ksr/p8x/hardware/control-card/kicad/README.md

# control-card -- KiCad

Generated by `generators/gen_kicad.py` from the canonical gen_eagle netlist
(`CARDS["control-card"]`), same standard as the memory card: 4-layer (F/B signals,
In1=GND, In2=VCC planes), a bypass cap above each IC, a labelled LED/jumper bank,
part values on silk. Routed with Freerouting. GENERATORS ARE CANON -- edit
`gen_kicad.py` and re-run `generators/build_kicad_card.sh control-card`.

| File | What |
|---|---|
| `p8x-control-card.kicad_pcb` | the board |
| `p8x-control-card.ses` | the Freerouting routing |
| `p8x-control-card-gerbers.zip` | orderable gerbers |
| `p8x-control-card-placement.pdf` | parts placement (refs+values) |
| `p8x-control-card-render-top.png` / `-3d.png` | renders |

Exotic parts use the closest standard KiCad footprint (flagged when built).
