ksr/p8x/fpga/tang-nano-20k/sdram/README.md

# SDRAM — Stage 0: does the in-package SDRAM work under the open flow?

The GW2AR-18's `R` is 64 Mbit of SDRAM in the same package, unused since the
microcode-compaction trick made it unnecessary for the 64K memory map. The
graphics framebuffer is the first thing that genuinely cannot fit in block RAM:
6 spare BSRAM blocks are 12288 bytes and the panel's own 480x272 needs 16320 at
even 1 bpp, so the current 240x136 2 bpp framebuffer is pixel-doubled to fill the
screen. Full resolution is an SDRAM project. This directory is the experiment.

## Finding 1: the SDRAM pads need NO `.cst` entries (verified 2026-08-17)

They are bonded inside the package, and **apicula/nextpnr special-cases the
magic port names**, exactly as Gowin EDA does. Verified by controlled experiment
rather than by reading about it:

| top-level port | result |
|---|---|
| `O_sdram_addr[10:0]` | placed, no constraint given |
| `O_notmagic_addr[10:0]` (same net, renamed) | `ERROR: Unconstrained IO` |

That control matters: nextpnr treats unconstrained IO as a hard error (it threw
exactly that for a mis-typed `led[4]`), so "placed without a constraint" can only
mean the name is recognised. A trivial design with all 55 SDRAM signals placed
clean at 30 IOBs for the control/address lines plus 32 `IOBUF`s for the data bus.

The magic names, which must appear verbatim on the top-level module:

```verilog
output        O_sdram_clk, O_sdram_cke, O_sdram_cs_n,
output        O_sdram_cas_n, O_sdram_ras_n, O_sdram_wen_n,
inout  [31:0] IO_sdram_dq,      // 32 bits wide, not 16
output [10:0] O_sdram_addr,
output [1:0]  O_sdram_ba,
output [3:0]  O_sdram_dqm
```

## Finding 2: it works (verified on hardware 2026-08-17)

`sdram_test.v` reports `SDRAM SEQ=0000 SPR=0000 PASS` on the board:

- 64 KB written and read back byte for byte, no errors
- a sparse pass touching one byte every 64 KB across the **whole 8 MB**, no
  errors -- so no address aliasing: rows, columns and banks are wired as
  expected and high addresses do not fold onto low ones
- refresh held throughout, the two passes being separated by the entire write
  phase

Costs, which was the other half of what stage 0 was for:

| | |
|---|---|
| LUT4 | 916 / 20736 (4%) -- controller **plus** test FSM **plus** UART |
| BSRAM | **0 / 46** |
| Fmax | 147 MHz against the 27 MHz it runs at |

The zero BSRAM is the important one. An SDRAM framebuffer does not add pressure
to a design already at 44/46 -- it *returns* the four blocks the current
framebuffer occupies, minus whatever a scanout line buffer needs (one block
holds a 2048-byte line, which is more than a 480-pixel line needs at any depth
we would pick).

### Bandwidth is not the constraint either

At 27 MHz the 32-bit bus is ~108 MB/s peak. Scanout needs:

| mode | bytes/frame | at 54.11 Hz | % of peak |
|---|---|---|---|
| 480x272 @ 4 bpp | 65,280 | 3.5 MB/s | 3% |
| 480x272 @ 8 bpp | 130,560 | 7.1 MB/s | 7% |

So the drawing engine keeps well over 90% of the bus even at 256 colours. What
is left to prove is **latency**, not throughput: SDRAM cannot promise a byte on
demand the way block RAM does, and a scanout cannot stall. That is stage 1.

## Finding 3: a scanout can live off SDRAM (verified on hardware 2026-08-17)

`sdram_video_test.v` puts a 480x272 8-bpp image on the panel, fetched line by
line from SDRAM. Confirmed on the board: the picture is correct -- border,
both diagonals and the fine horizontal ramp all as designed, so line addressing,
stride and the 32-bit byte lanes are all right.

| | stage 1 | today's BSRAM framebuffer |
|---|---|---|
| LUT4 | 835 / 20736 (4%) | -- |
| BSRAM | **1** (the line buffer) | **4** |
| Fmax | 200 MHz | -- |

**Four times the resolution and 64 times the colours, for three FEWER block
RAMs.** That inverts the trade-off this started from: the SDRAM path is not a
way to spend resources to get resolution, it is a way to get resolution and hand
resources back to a design that was at 44/46 and on a placement cliff.

(The cliff itself turned out to have a second, larger cause that had nothing to
do with graphics — the SD sector buffer inferring 4,096 flip-flops. With both
fixed the `lcd` build sits at 7226/20736 LUT4 and 42/46 BSRAM. See
[HANDOFF.md](HANDOFF.md).)

### Still to confirm

The `underruns` counter is the real measurement and has only been eyeballed, not
watched over a long run. It should be read as "UR=0000 with FR climbing" over
minutes, not seconds, before this is called settled -- and re-checked once a
drawing engine is competing for the same bus, which is the case that matters.

Stage 1 was also NOT simulated before loading, unlike stage 0. That is a gap: the
stage 0 bench caught two real bugs, and the same discipline should be applied
here before any of this is merged toward the P8X design.

## What this does and does not prove

It proves the toolchain will *wire up* the SDRAM. It says nothing yet about
whether we can meet its timing, which is the actual risk: SDRAM has refresh, row
activation and CAS latency, so unlike block RAM it cannot promise a byte on
demand — and a video scanout cannot stall. That is what the rest of Stage 0 and
Stage 1 are for.

## Reference

`nand2mario/sdram-tang-nano-20k` (Apache 2.0) is a known-good 32-bit controller
for this exact board: 64.8 MHz, 4-cycle read latency, byte-addressable interface.
It targets Gowin EDA and instantiates the `Gowin_rPLL` IP wrapper, so an open-flow
port would instantiate the `rPLL` primitive directly.
