ksr/p8x/BACKLOG-DONE.md

# P8X Backlog — Completed

<!-- migrated from BACKLOG.md 2026-09-14 (category review: [x] done items belong here) -->

<!-- 2026-10-02: hardware items closed by the KiCad flow, and the 2026-09-16 overnight batch -->

- [x] **Publish the project website (2026-10-02).** `website/` builds the site
      from these documents (MkDocs + Material; `sh website/build.sh publish` is a
      strict build), and `.github/workflows/website.yml` builds it on every push to
      `main` and, with deploy switched on (2026-10-02), publishes it to
      https://p8x.cottageworker.com. The visitor status page is
      `docs/p8x-status.md`; keep it current with BACKLOG.md.
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
