ksr/p8x/GLOSSARY.md

# P8X Glossary — acronyms & signals

A reference for the abbreviations, signal names, and register/bus terms used
across the P8X project. Authoritative sources where a term has one:
- control word / opcodes → `microcode/genucode.py`
- bus pinout → `hardware/backplane/p8x-bus-definition.md`
- monitor/BIOS ABI → `docs/p8x-monitor.md`
- parts → `hardware/p8x-bom.csv` (from `generators/gen_bom.py`)

---
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
