ksr/p8x/hardware/alu-card/kicad/p8x-alu-card-render-top.png

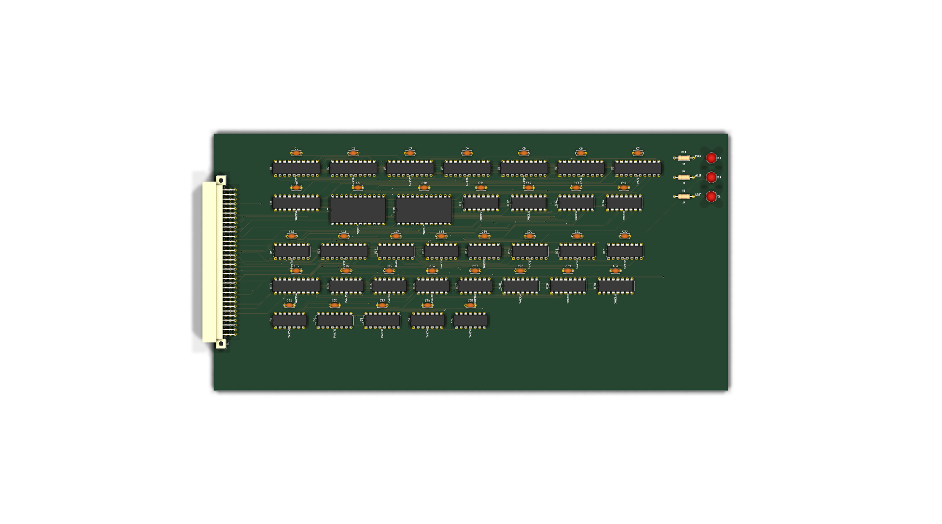
hardware/alu-card/kicad/p8x-alu-card-render-top.png
