ksr/p8x/hardware/backplane/kicad/p8x-backplane-render-3d.png

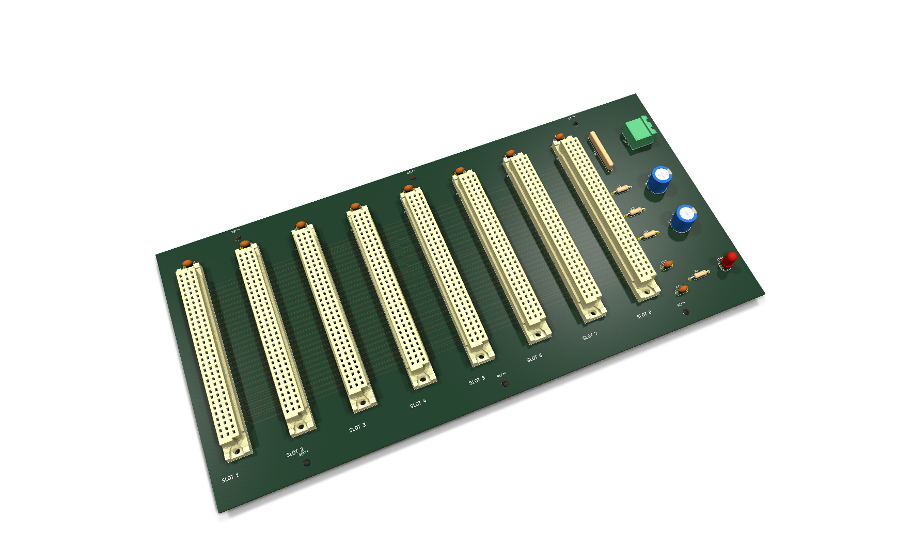
hardware/backplane/kicad/p8x-backplane-render-3d.png
