ksr/p8x/hardware/memory-card/kicad/p8x-memory-card-render-3d.png

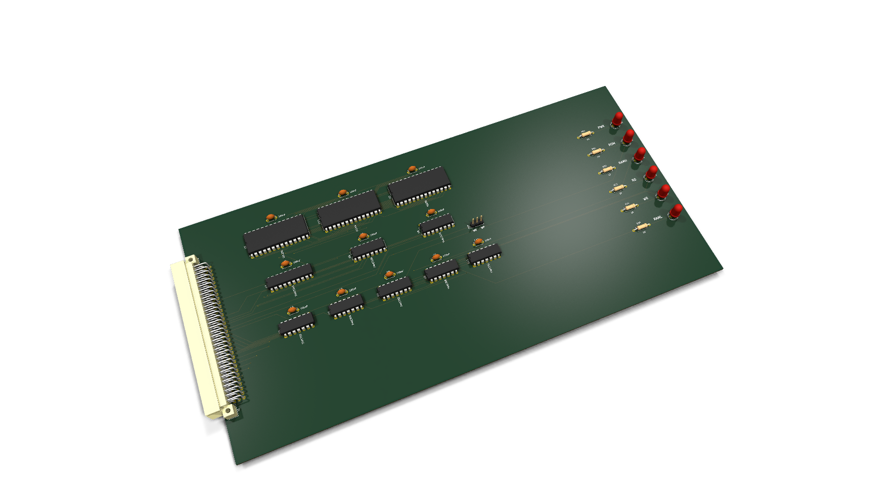
hardware/memory-card/kicad/p8x-memory-card-render-3d.png
