ksr/p8x/hardware/parked/peripheral-card/kicad/p8x-peripheral-card-render-3d.png

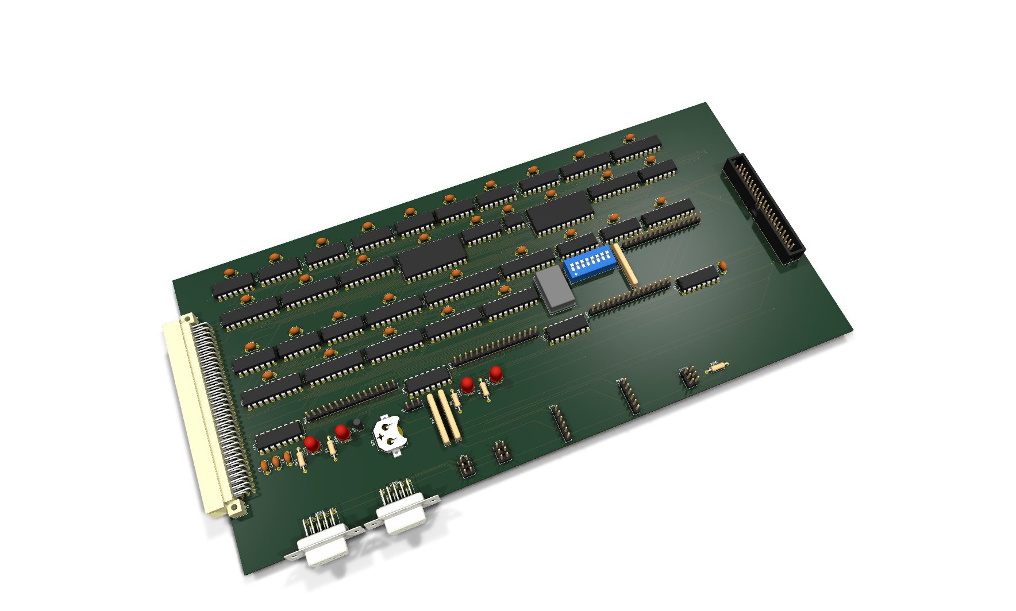
hardware/parked/peripheral-card/kicad/p8x-peripheral-card-render-3d.png
