ksr/p8x/hardware/regbank-card/kicad/p8x-regbank-card-render-top.png

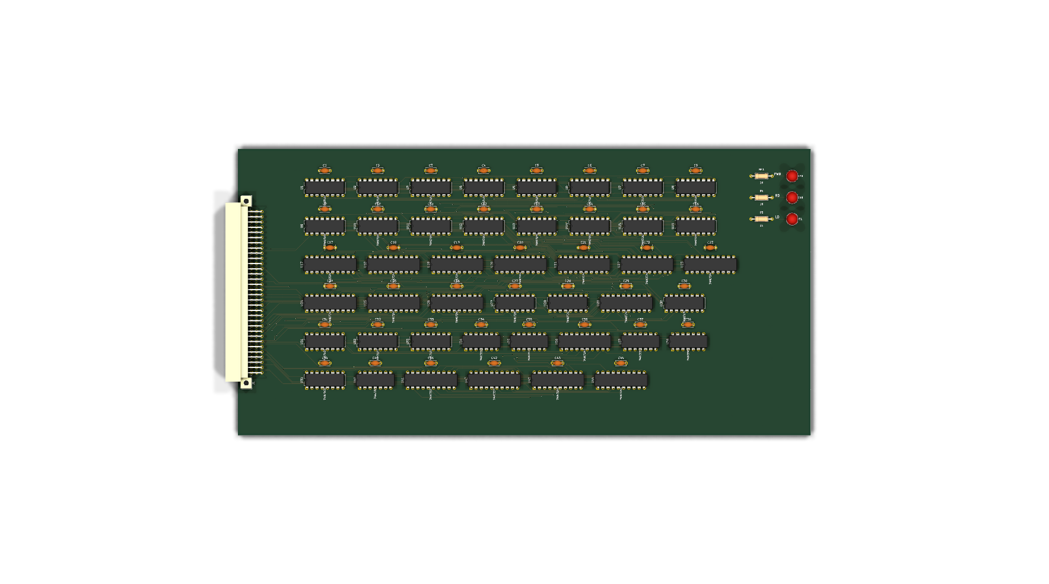
hardware/regbank-card/kicad/p8x-regbank-card-render-top.png
