ksr/p8x/website/p8x-collage.jpg

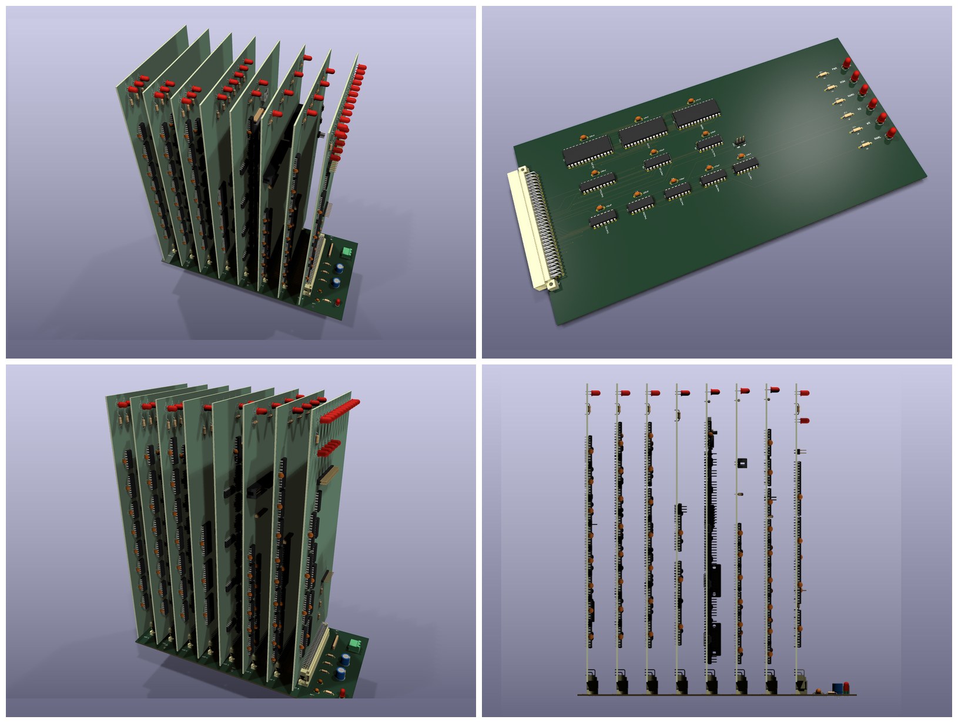
website/p8x-collage.jpg
