ksr/p8x/hardware/cf-card/p8x-cf-card-placement.pdf

U1 74HCT245 | C1 | U2 74HCT30 | C2 | U3 74HCT138 | C3 | U4 74HCT138 | C4 | U5 74HCT14 | C5 | U6 74HCT10 | C6 | U7 74HCT10 | C7 | U8 74HCT08 | C8

# P8X CF-IDE CARD REV A - 8-BIT TRUE IDE AT 0xFF10

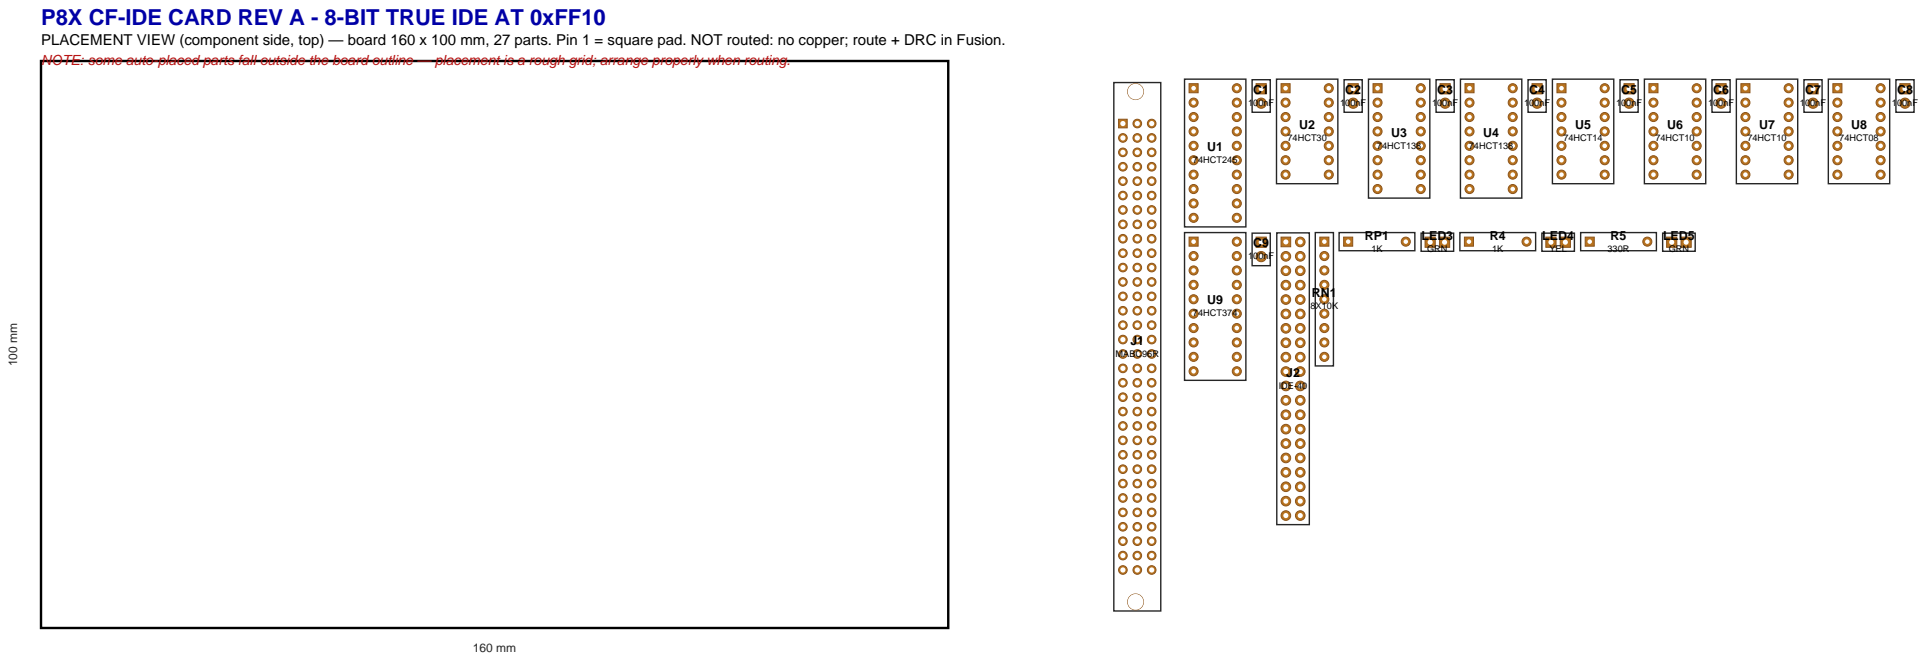
[picture p26: page 1]

PLACEMENT VIEW (component side, top) — board 160 x 100 mm, 27 parts. Pin 1 = square pad. NOT routed: no copper; route + DRC in Fusion.
NOTE: some auto-placed parts fall outside the board outline — placement is a rough grid; arrange properly when routing.

U9 74HCT374 | C9 | | 1K | LED3 GRN | 1K | LED4 YEL | 330R | LED5 GRN
