ksr/p8x/hardware/control-card/p8x-control-card-placement.pdf

U1 74HCT161 | C2 | U2 74HCT14 | C3 | U3 74HCT74 | C4 | U4 74HCT00 | C5 | U5 74HCT08 | C6 | U6 74HCT32 | C7 | U7 74HCT377 | C8 | U8 74HCT138 | C9

# P8X CONTROL/MICROCODE CARD REV B

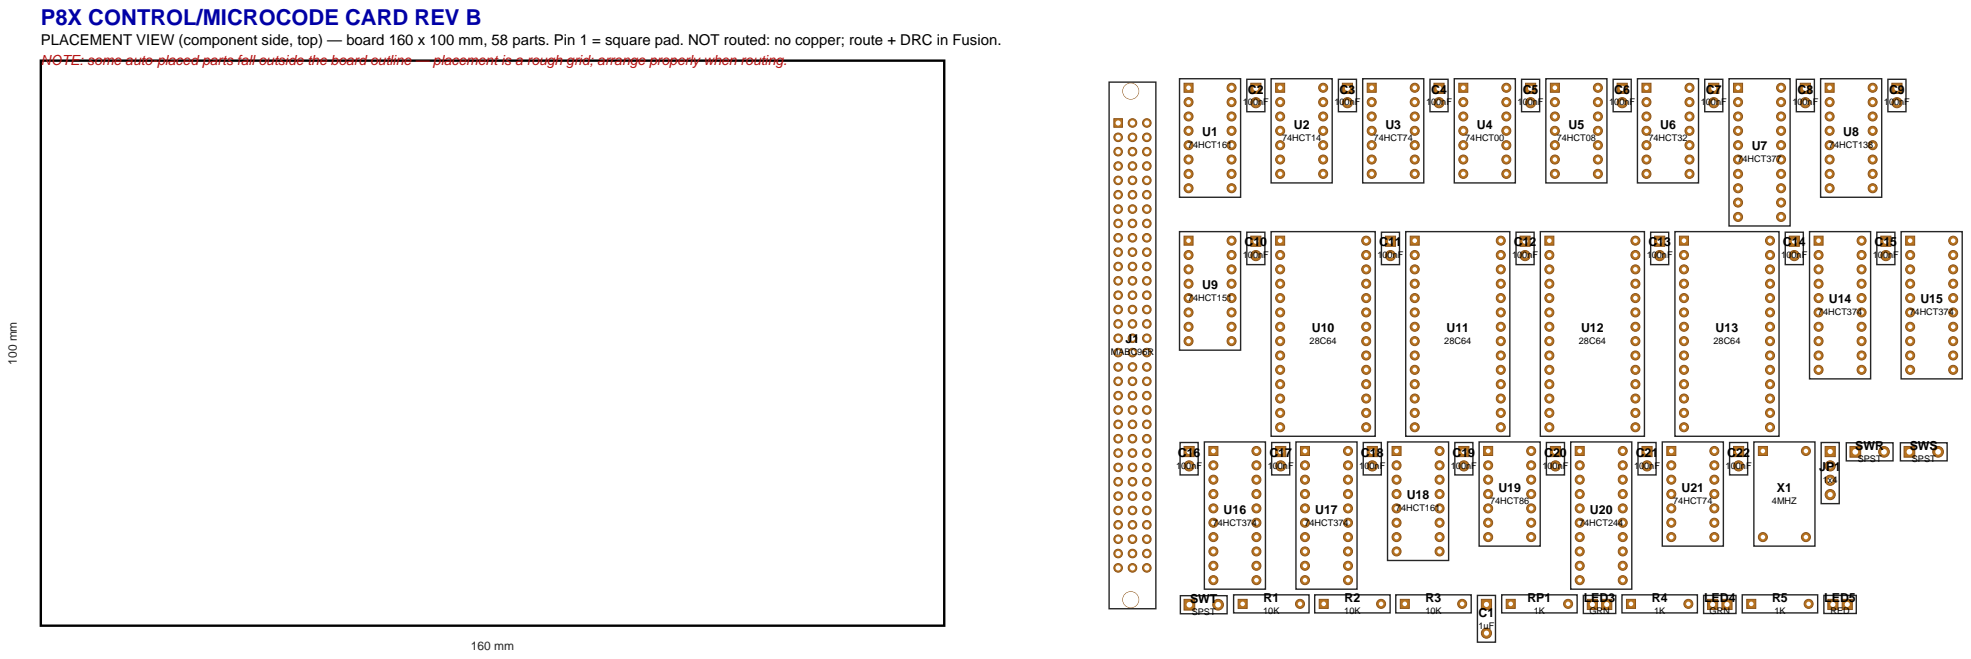
[picture p27: page 1]

PLACEMENT VIEW (component side, top) — board 160 x 100 mm, 58 parts. Pin 1 = square pad. NOT routed: no copper; route + DRC in Fusion.
NOTE: some auto-placed parts fall outside the board outline — placement is a rough grid; arrange properly when routing.

U9 74HCT151 | C10 | U10 28C64 | C11 | | U11 28C64 | C12 | U12 28C64 | C13 | U13 28C64 | C14 | 74HCT374 | U14 | C15 | 74HCT374 | U15
