ksr/p8x/hardware/control-card/p8x-control-card-schematic.pdf

# P8X CONTROL/MICROCODE CARD REV B - traditional wiring (auto-drafted)

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

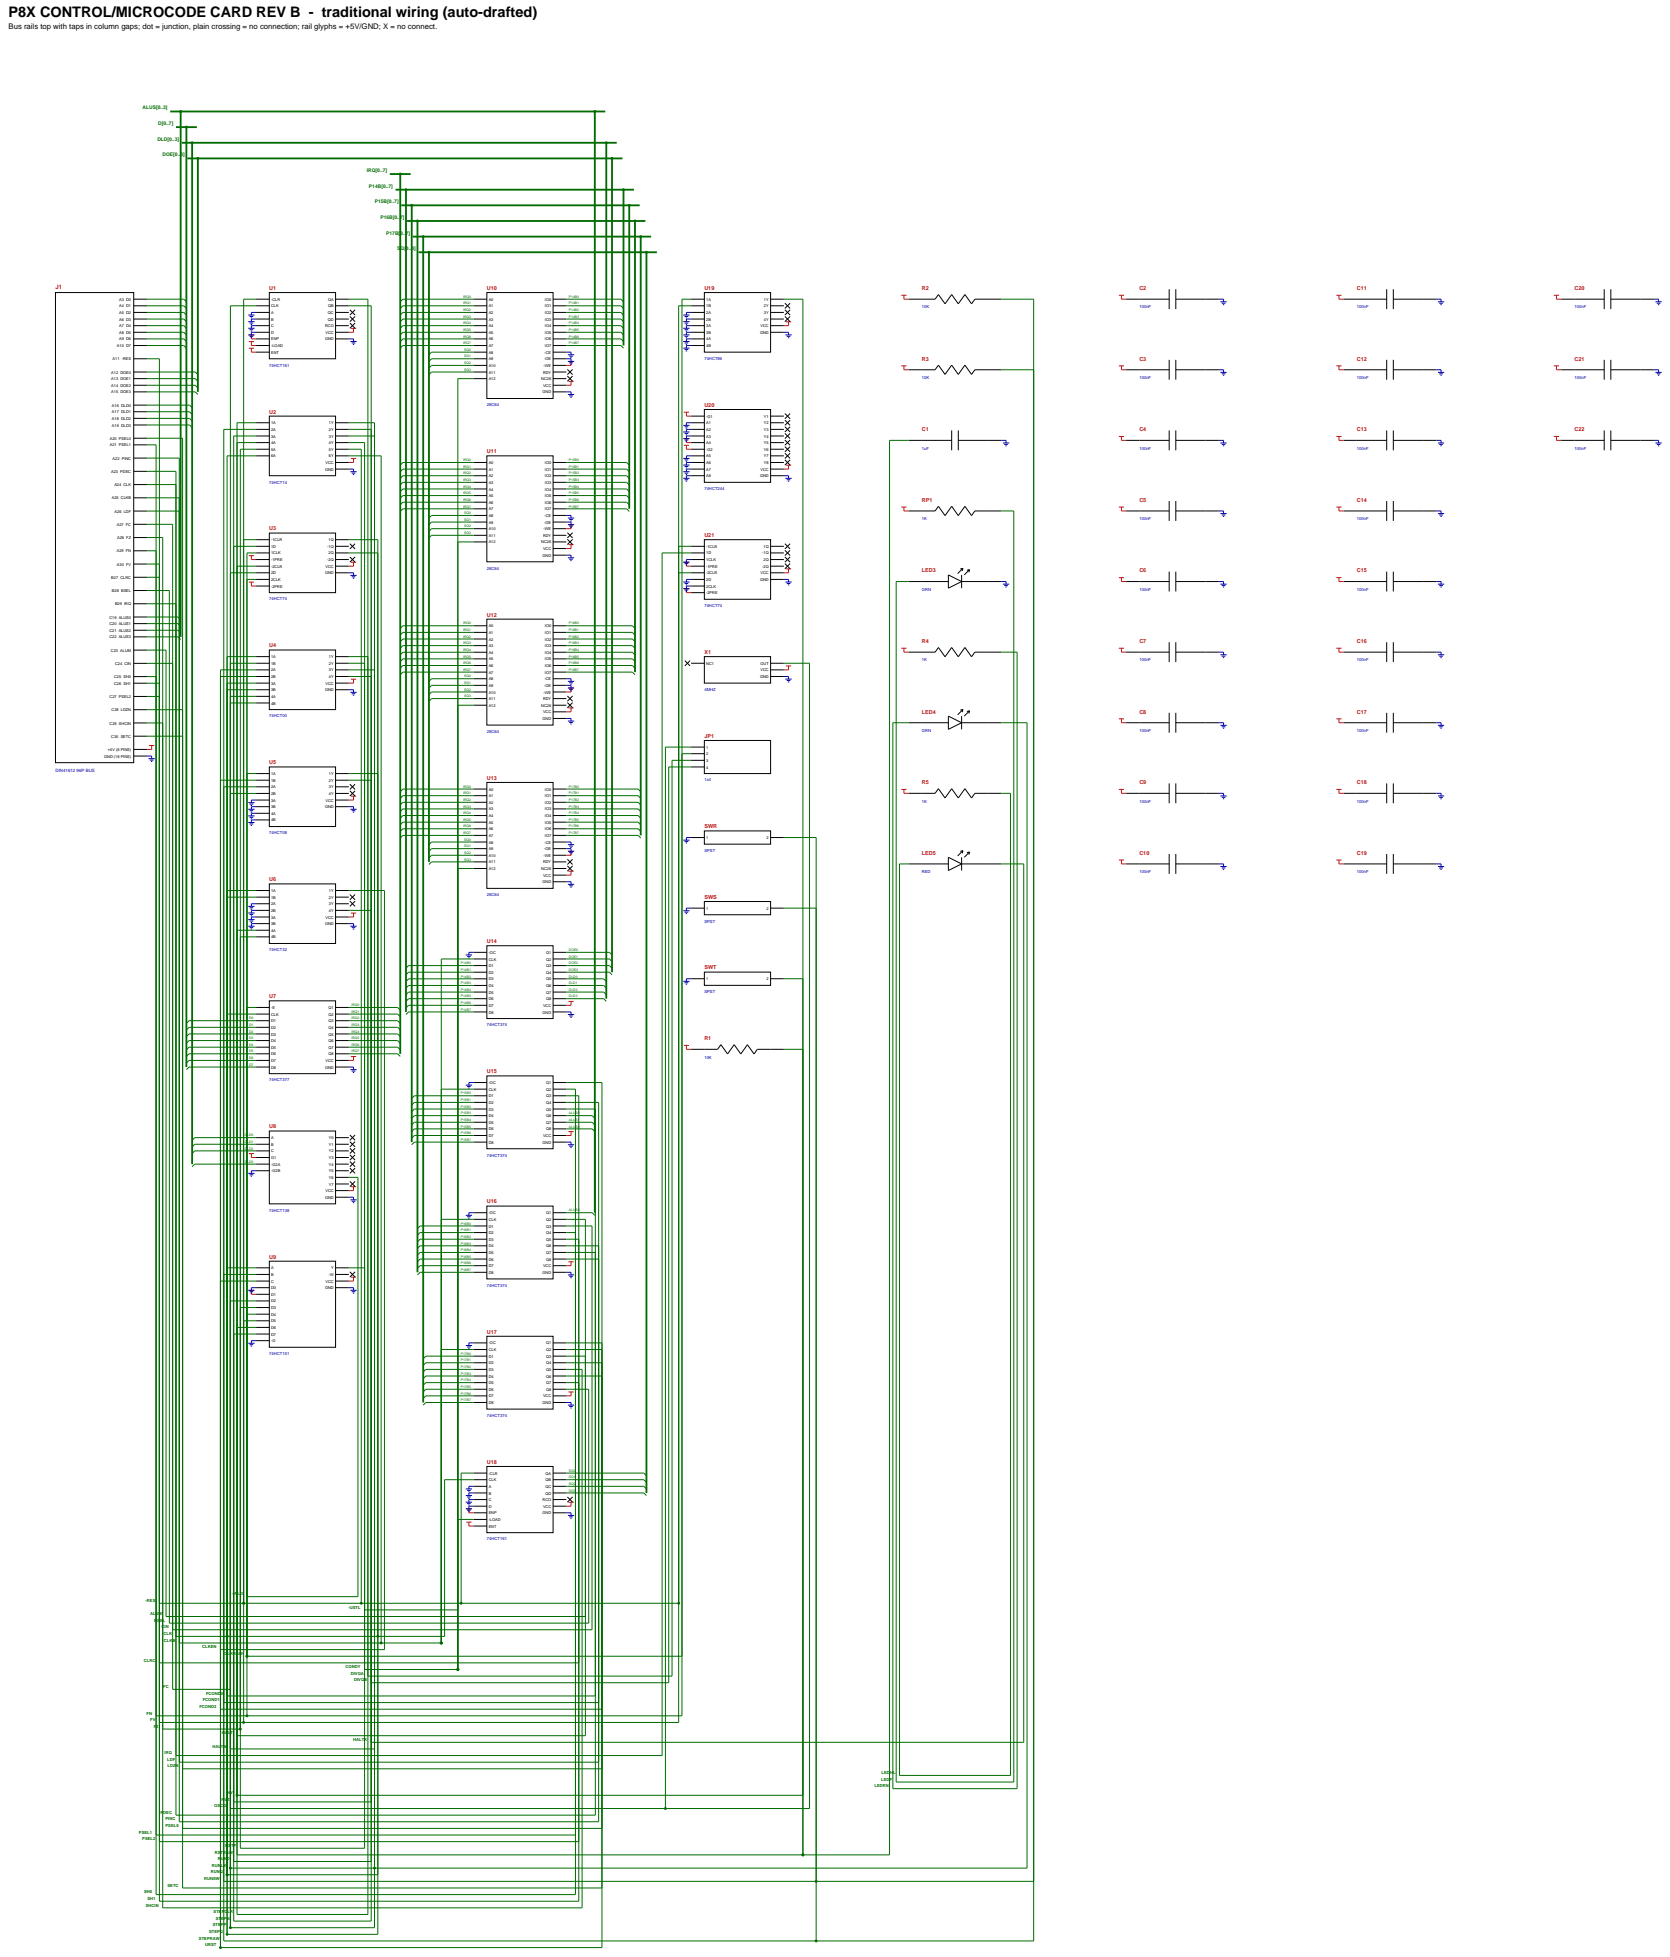
[picture p28: page 1]

CLKEN

CONDY DIVQA DIVQB
