ksr/p8x/hardware/io-card/p8x-io-card-placement.pdf

U1 74HCT30 | C6 | U2 74HCT138 | C7 | U3 74HCT138 | C8 | U4 74HCT138 | C9 | U5 74HCT32 | C10 | U6 74HCT08 | C11 | U7 74HCT161 | C12 | U8 MAX232 | C13

# P8X I/O CARD REV A - ACIA + SWITCHES + LEDS + BUS MONITOR

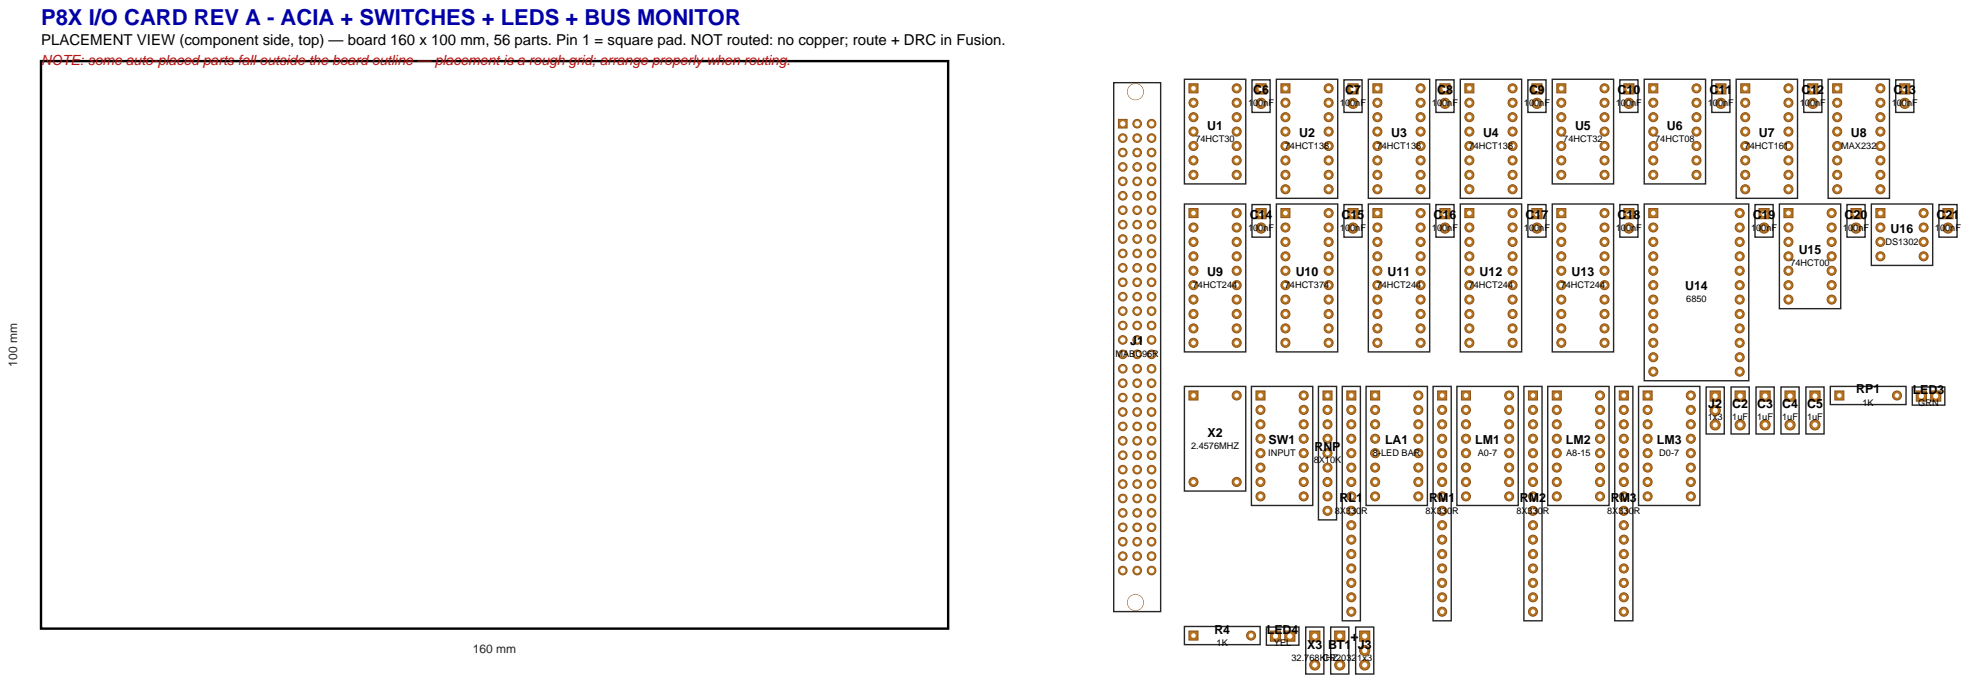
[picture p29: page 1]

PLACEMENT VIEW (component side, top) — board 160 x 100 mm, 56 parts. Pin 1 = square pad. NOT routed: no copper; route + DRC in Fusion.
NOTE: some auto-placed parts fall outside the board outline — placement is a rough grid; arrange properly when routing.

U9 74HCT244 | U10 74HCT374 | U11 74HCT244 | U12 74HCT244 | U13 74HCT244 | U14 6850 | U15 74HCT00 | U16 DS1302

C14 | C15 | C16 | C17 | C18 | C19 | C20 | C21
100nF | 100nF | 100nF | 100nF | 100nF | 100nF | 100nF | 100nF

X2 2.4576MHZ | SW1 | LA1 8-LED BAR | | LM1 A0-7 | LM2 A8-15 | | | LM3 D0-7 | J2 | C2 | C3 | C4 | C5 | RP1 1K | GRN
