ksr/p8x/hardware/led-card/p8x-led-card-placement.pdf

## P8X LED OUTPUT CARD (test - write-only 8 LEDs at $FF0C)

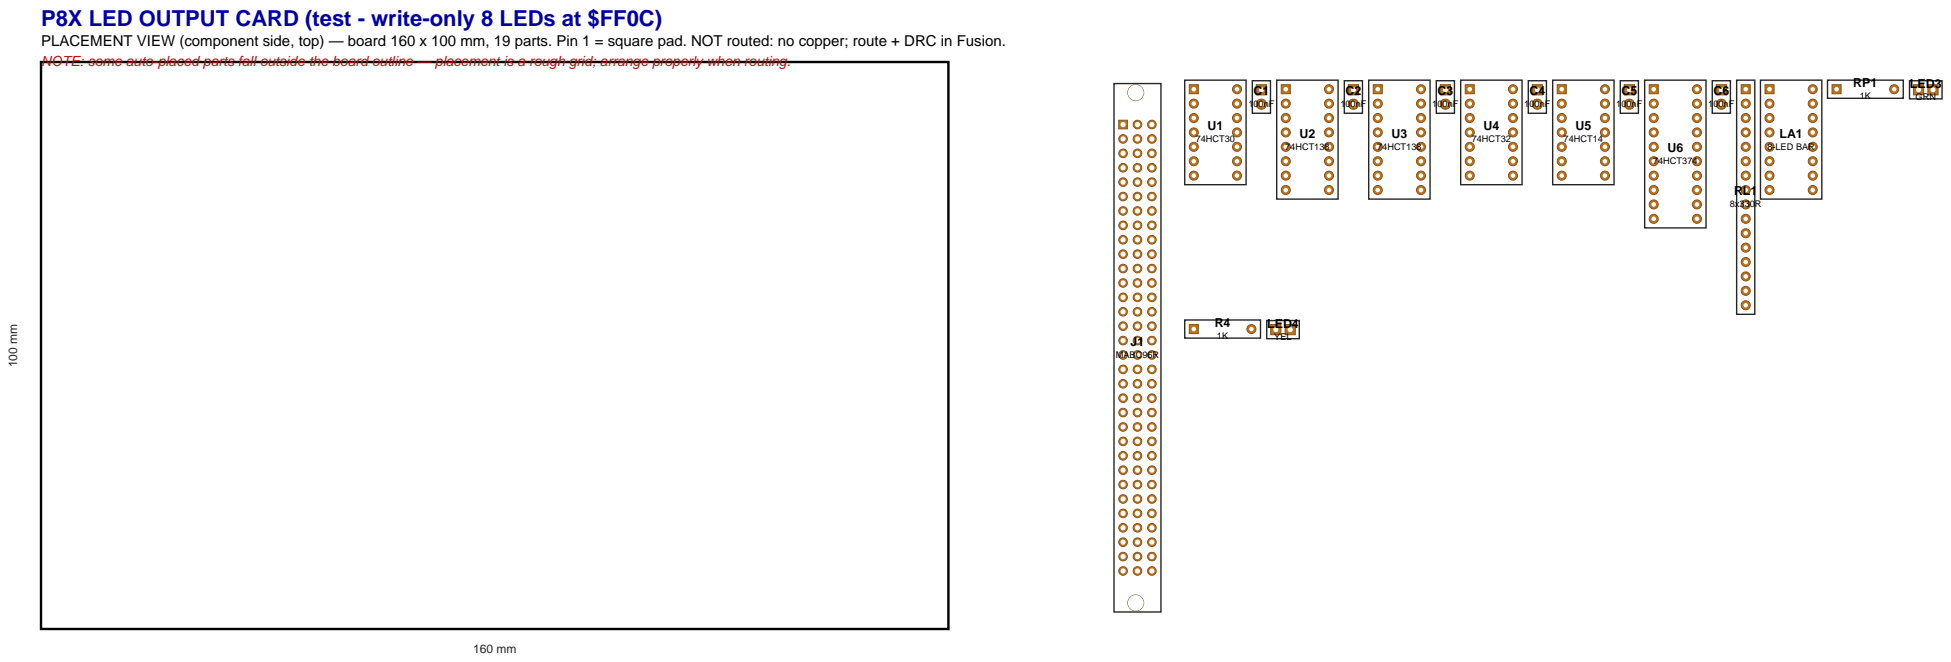
[picture p30: page 1]

PLACEMENT VIEW (component side, top) — board 160 x 100 mm, 19 parts. Pin 1 = square pad. NOT routed: no copper; route + DRC in Fusion.
NOTE: some auto-placed parts fall outside the board outline — placement is a rough grid; arrange properly when routing.

U1 74HCT30 | C1 | U2 74HCT138 | C2 | U3 74HCT138 | C3 | U4 74HCT32 | C4 | U5 74HCT14 | C5 | U6 74HCT374 | C6 | LA1 8-LED BAR | RP1 1K | LED3
