ksr/p8x/hardware/memory-card/p8x-memory-card-placement.pdf

U1 28C256 | C1 | U2 62256 | C2 | 74HCT245 | U3 | C3 | U4 74HCT30 | C4 | 74HCT138 | U5 | C5 | 74HCT138 | U6 | C6 | U7 74HCT00 | C7 | U8 74HCT32

# P8X MEMORY CARD REV E

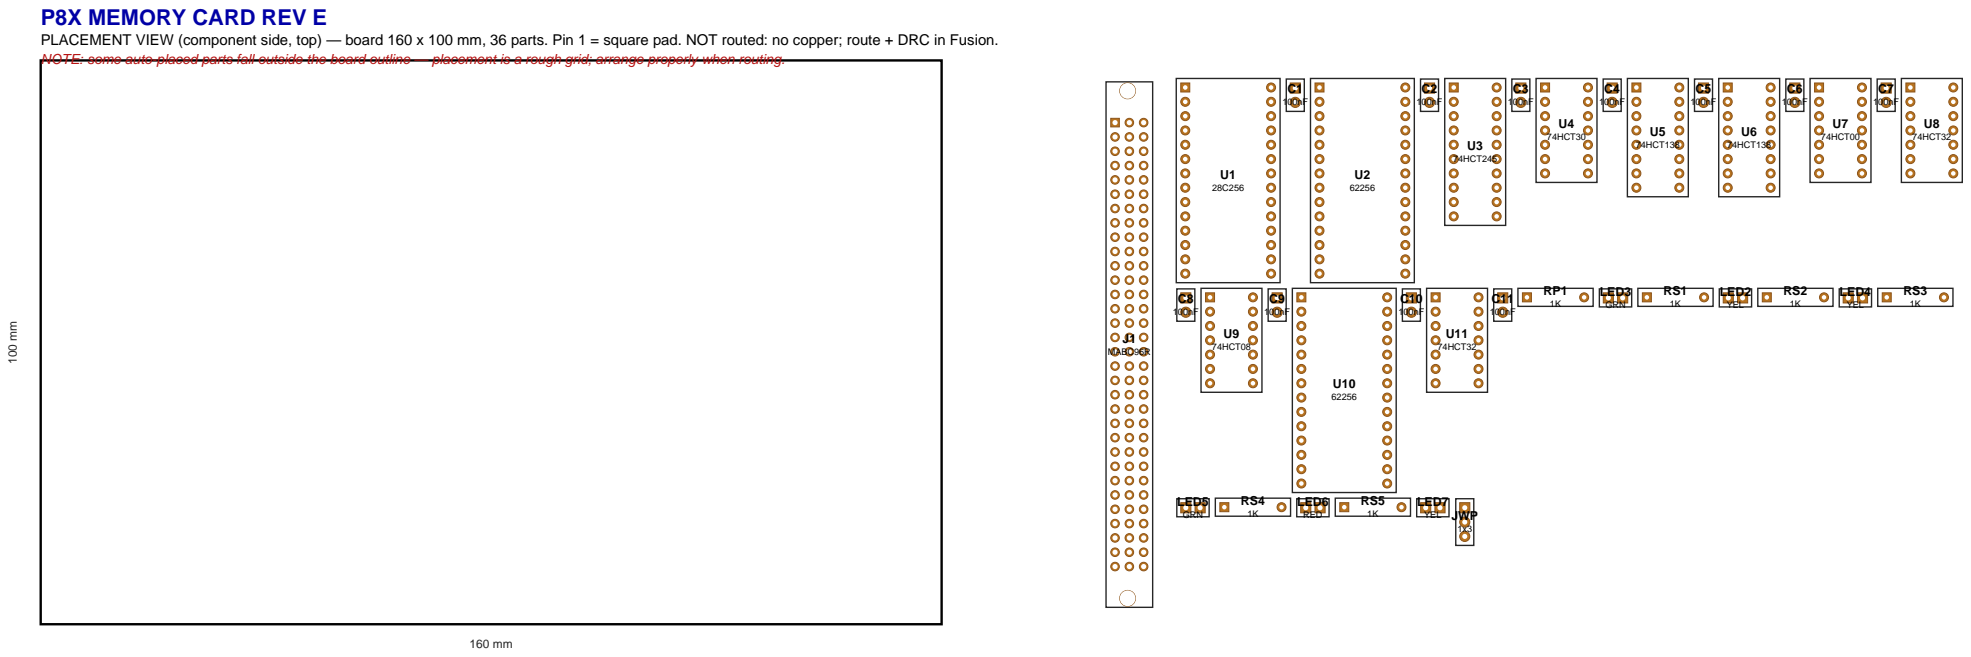
[picture p31: page 1]

PLACEMENT VIEW (component side, top) — board 160 x 100 mm, 36 parts. Pin 1 = square pad. NOT routed: no copper; route + DRC in Fusion.
NOTE: some auto-placed parts fall outside the board outline — placement is a rough grid; arrange properly when routing.
