ksr/p8x/hardware/regbank-card/p8x-regbank-card-placement.pdf

U1 74HCT169 | C1 | U2 74HCT169 | C2 | U3 74HCT169 | C3 | U4 74HCT169 | C4 | U5 74HCT169 | C5 | U6 74HCT169 | C6 | U7 74HCT169 | C7 | U8 74HCT169 | C8
C9 | C10 | C11 | C12 | C13 | C14 | C15 | C16

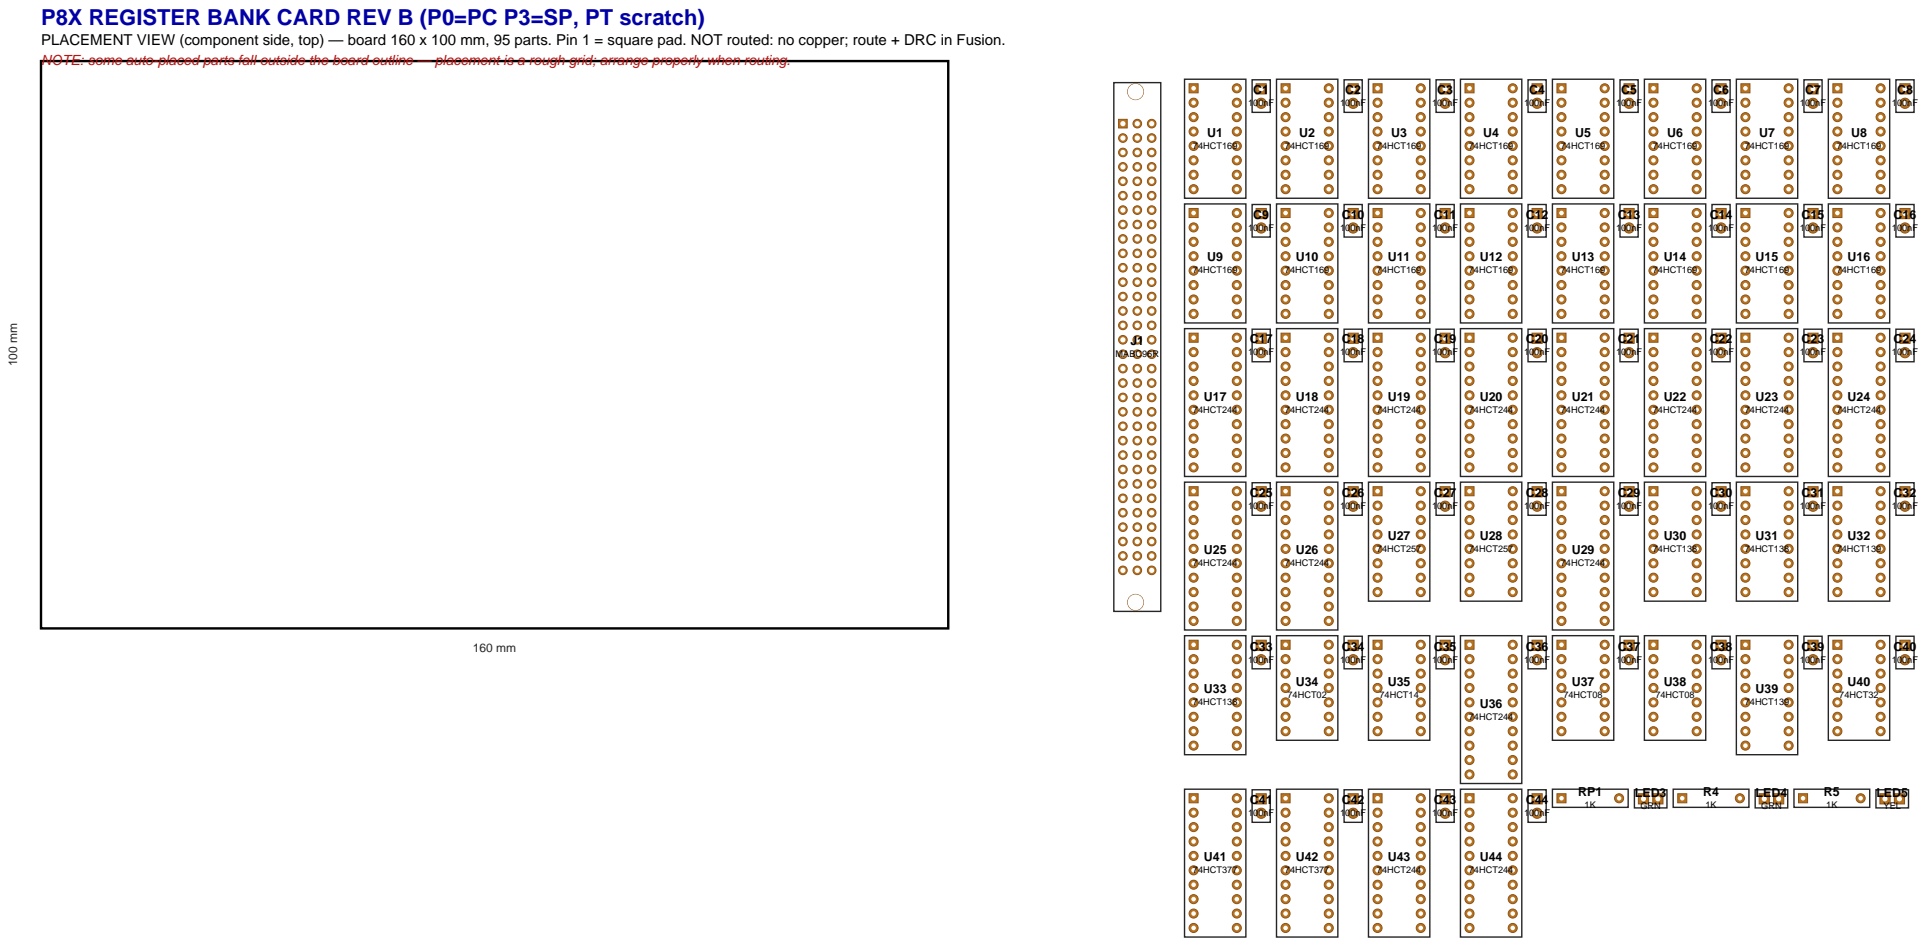
[picture p32: page 1]

P8X REGISTER BANK CARD REV B (P0=PC P3=SP, PT scratch)
PLACEMENT VIEW (component side, top) — board 160 x 100 mm, 95 parts. Pin 1 = square pad. NOT routed: no copper; route + DRC in Fusion.
NOTE: some auto-placed parts fall outside the board outline — placement is a rough grid; arrange properly when routing.

U9 74HCT169 | U10 74HCT169 | U11 74HCT169 | U12 74HCT169 | U13 74HCT169 | U14 74HCT169 | U15 74HCT169 | U16 74HCT169

U17 74HCT244 | C17 | U18 74HCT244 | C18 | U19 74HCT244 | C19 | U20 74HCT244 | C20 | U21 74HCT244 | C21 | U22 74HCT244 | C22 | U23 74HCT244 | C23 | U24 74HCT244 | C24

C25 | C26 | C27 | C28 | C29 | C30 | C31 | C32
100nF | 100nF | 100nF | 100nF | 100nF | 100nF | 100nF

U25 74HCT244 | U26 74HCT244 | U27 74HCT257 | U28 74HCT257 | U29 74HCT244 | U30 74HCT138 | U31 74HCT138 | U32 74HCT139

U33 74HCT138 | C33 | U34 74HCT02 | C34 | U35 74HCT14 | C35 | U36 74HCT244 | C36 | U37 74HCT08 | C37 | U38 74HCT08 | C38 | U39 74HCT139 | C39 | U40 74HCT32 | C40

U41 74HCT377 | C41 | U42 74HCT377 | C42 | U43 74HCT244 | C43 | U44 74HCT244 | C44 | 1K | LED3 GRN | 1K | LED4 GRN | 1K | LED5 YEL
