ksr/p8x/hardware/regbank-card/p8x-regbank-card-schematic.pdf

P8X REGISTER BANK CARD REV B (P0=PC P3=SP, PT scratch) - traditional wiring (auto-drafted)

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

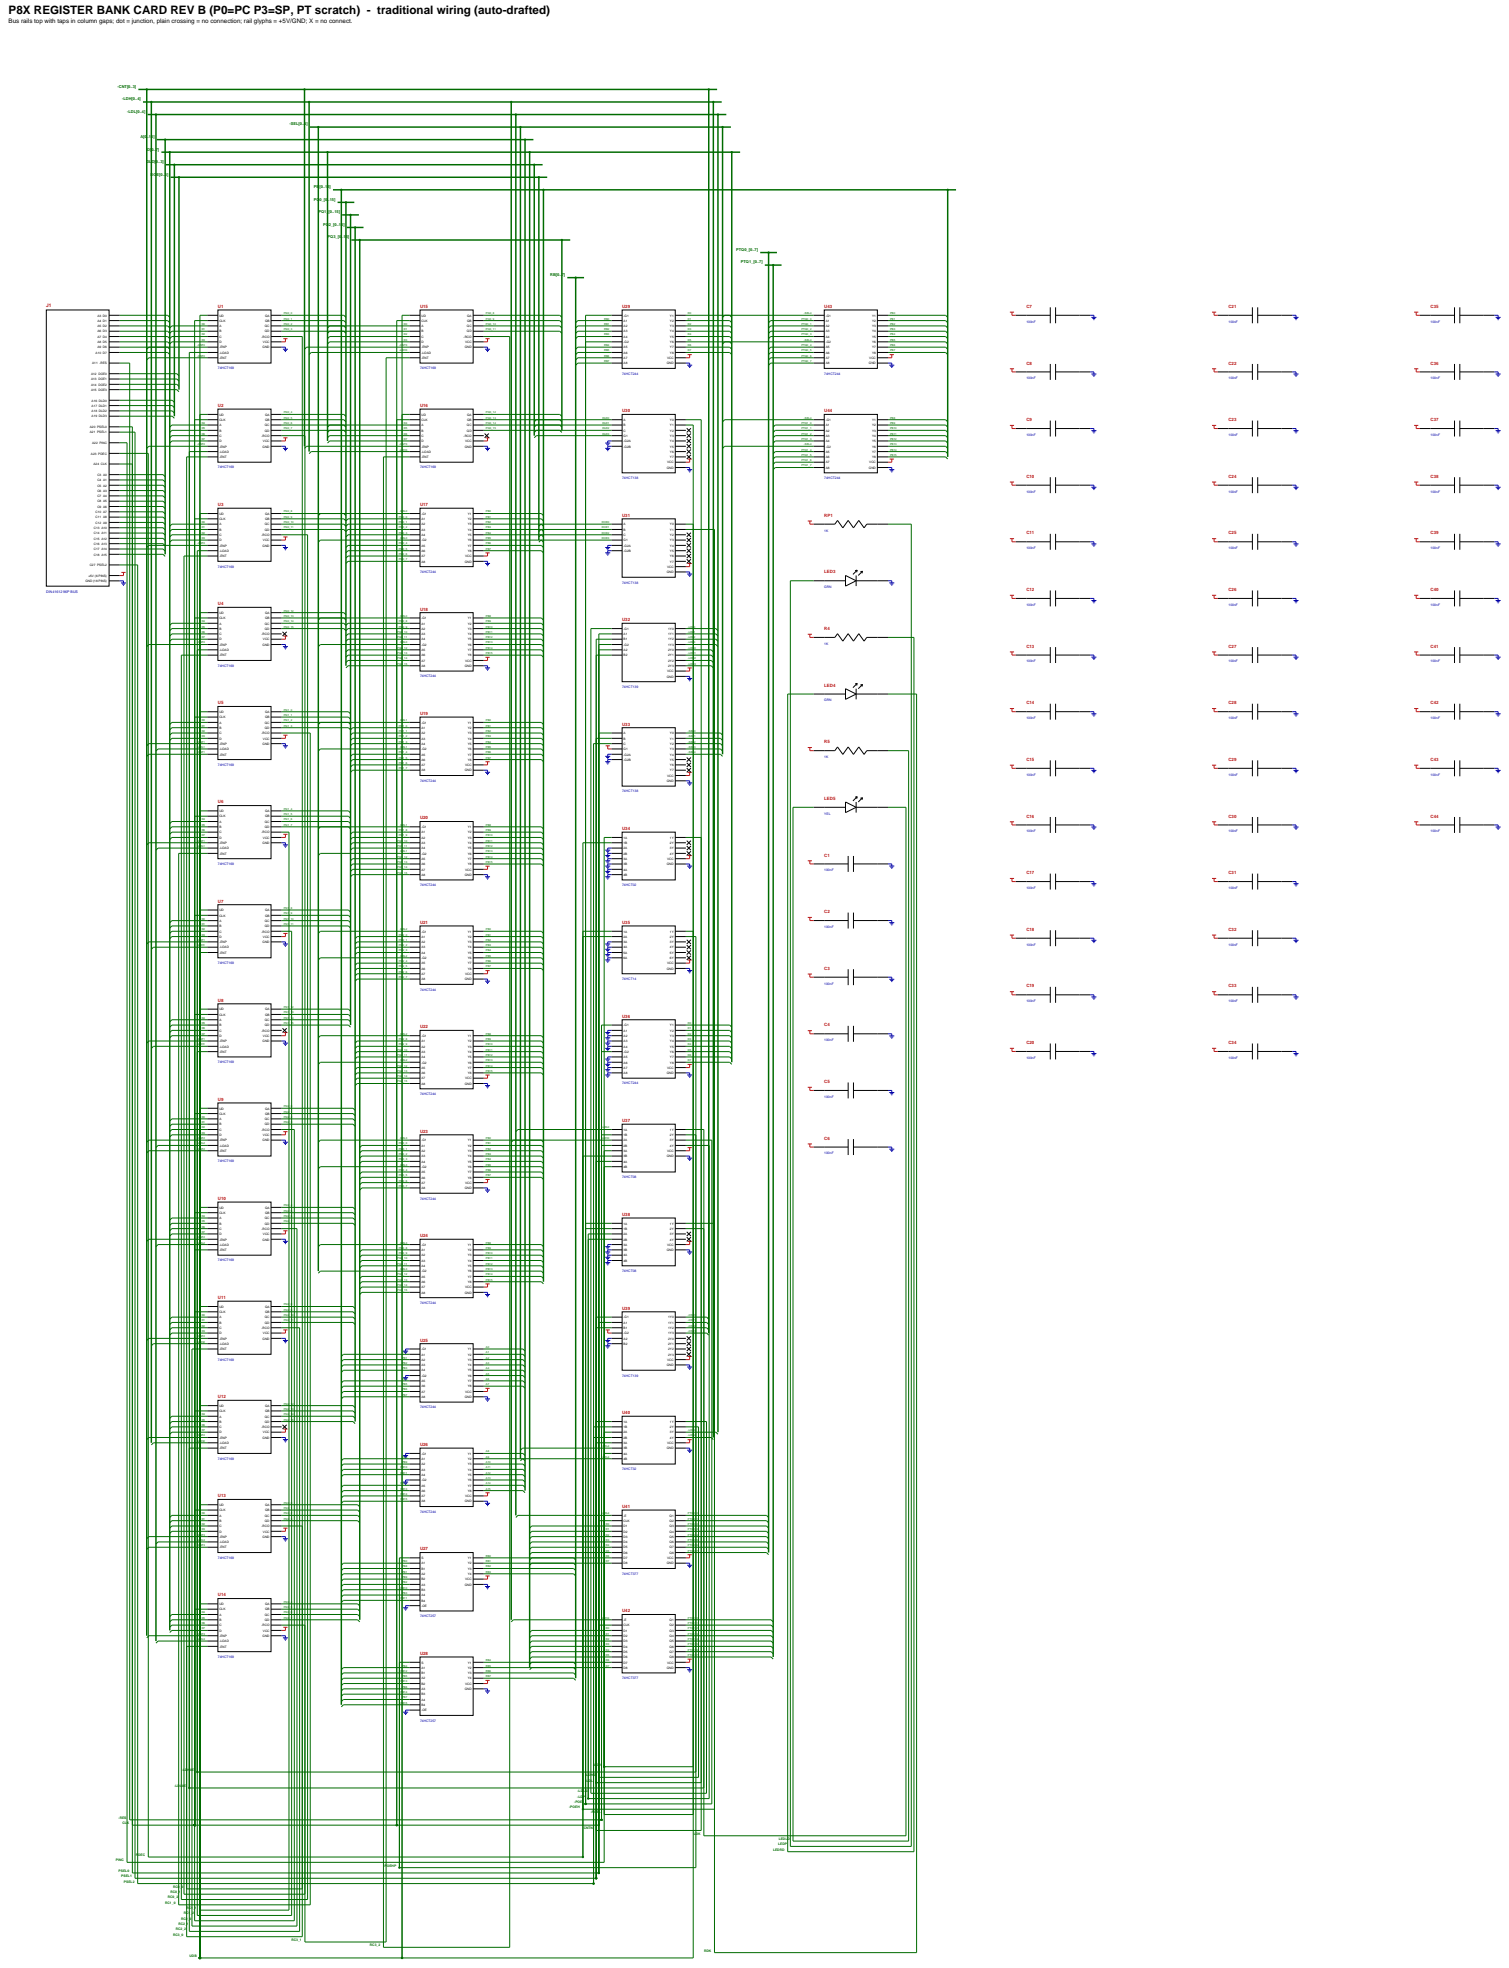
[picture p33: page 1]

-LDHG -LDL

-POE -POEH

-POEL
