ksr/p8x/hardware/backplane/p8x-backplane-placement.pdf

C1

C2

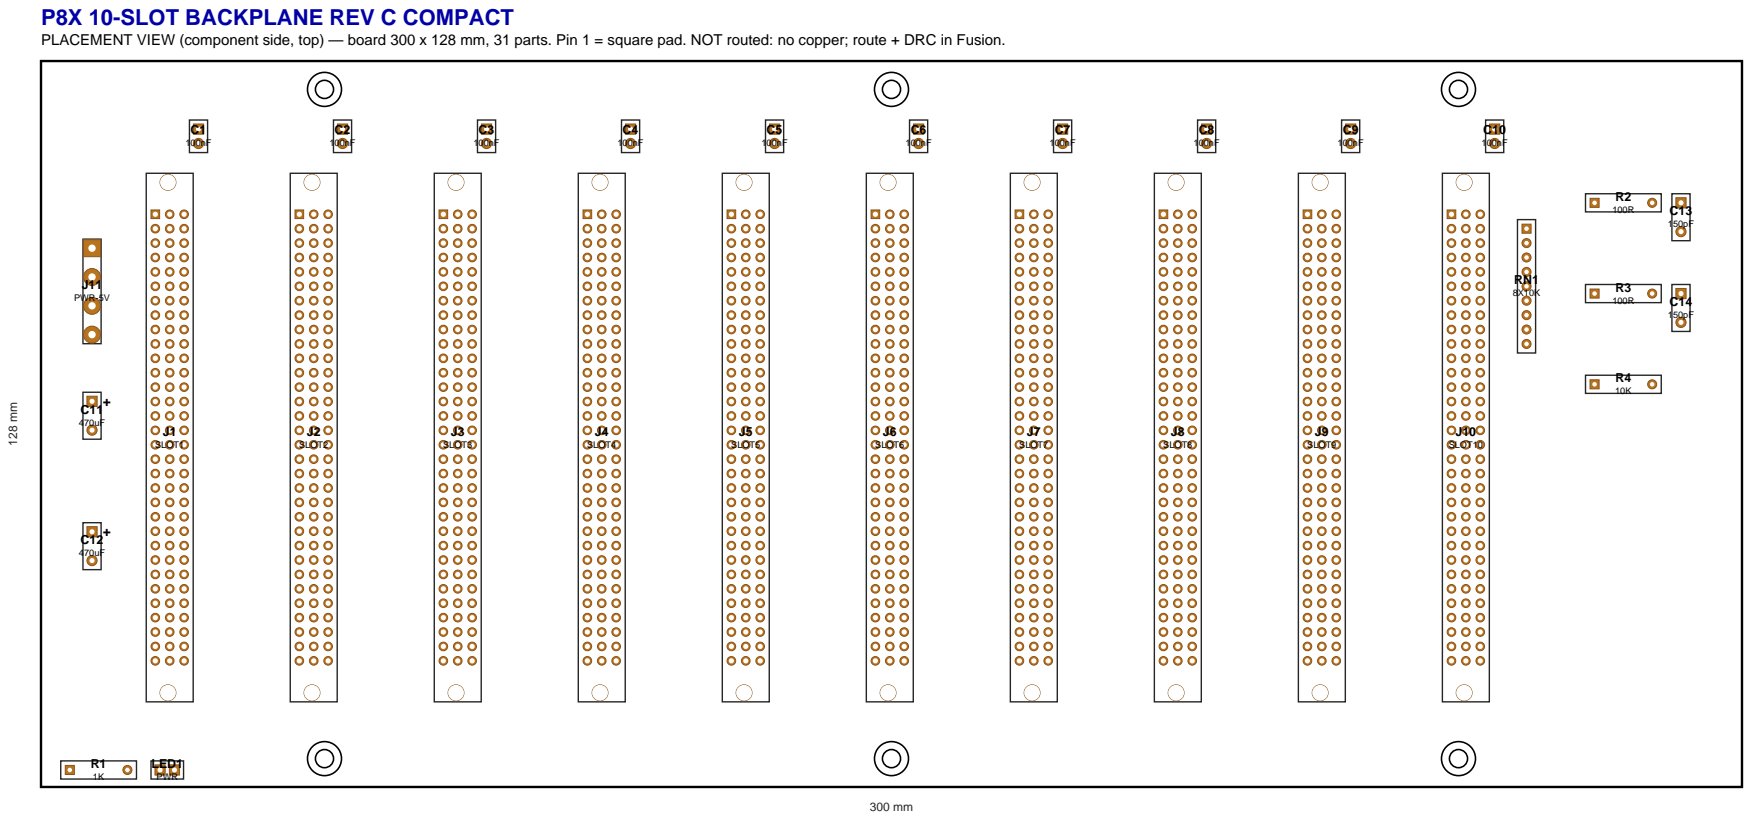
[picture p34: page 1]

P8X 10-SLOT BACKPLANE REV C COMPACT
PLACEMENT VIEW (component side, top) — board 300 x 128 mm, 31 parts. Pin 1 = square pad. NOT routed: no copper; route + DRC in Fusion.
