ksr/p8x/hardware/cf-card/kicad/p8x-cf-card-placement.pdf

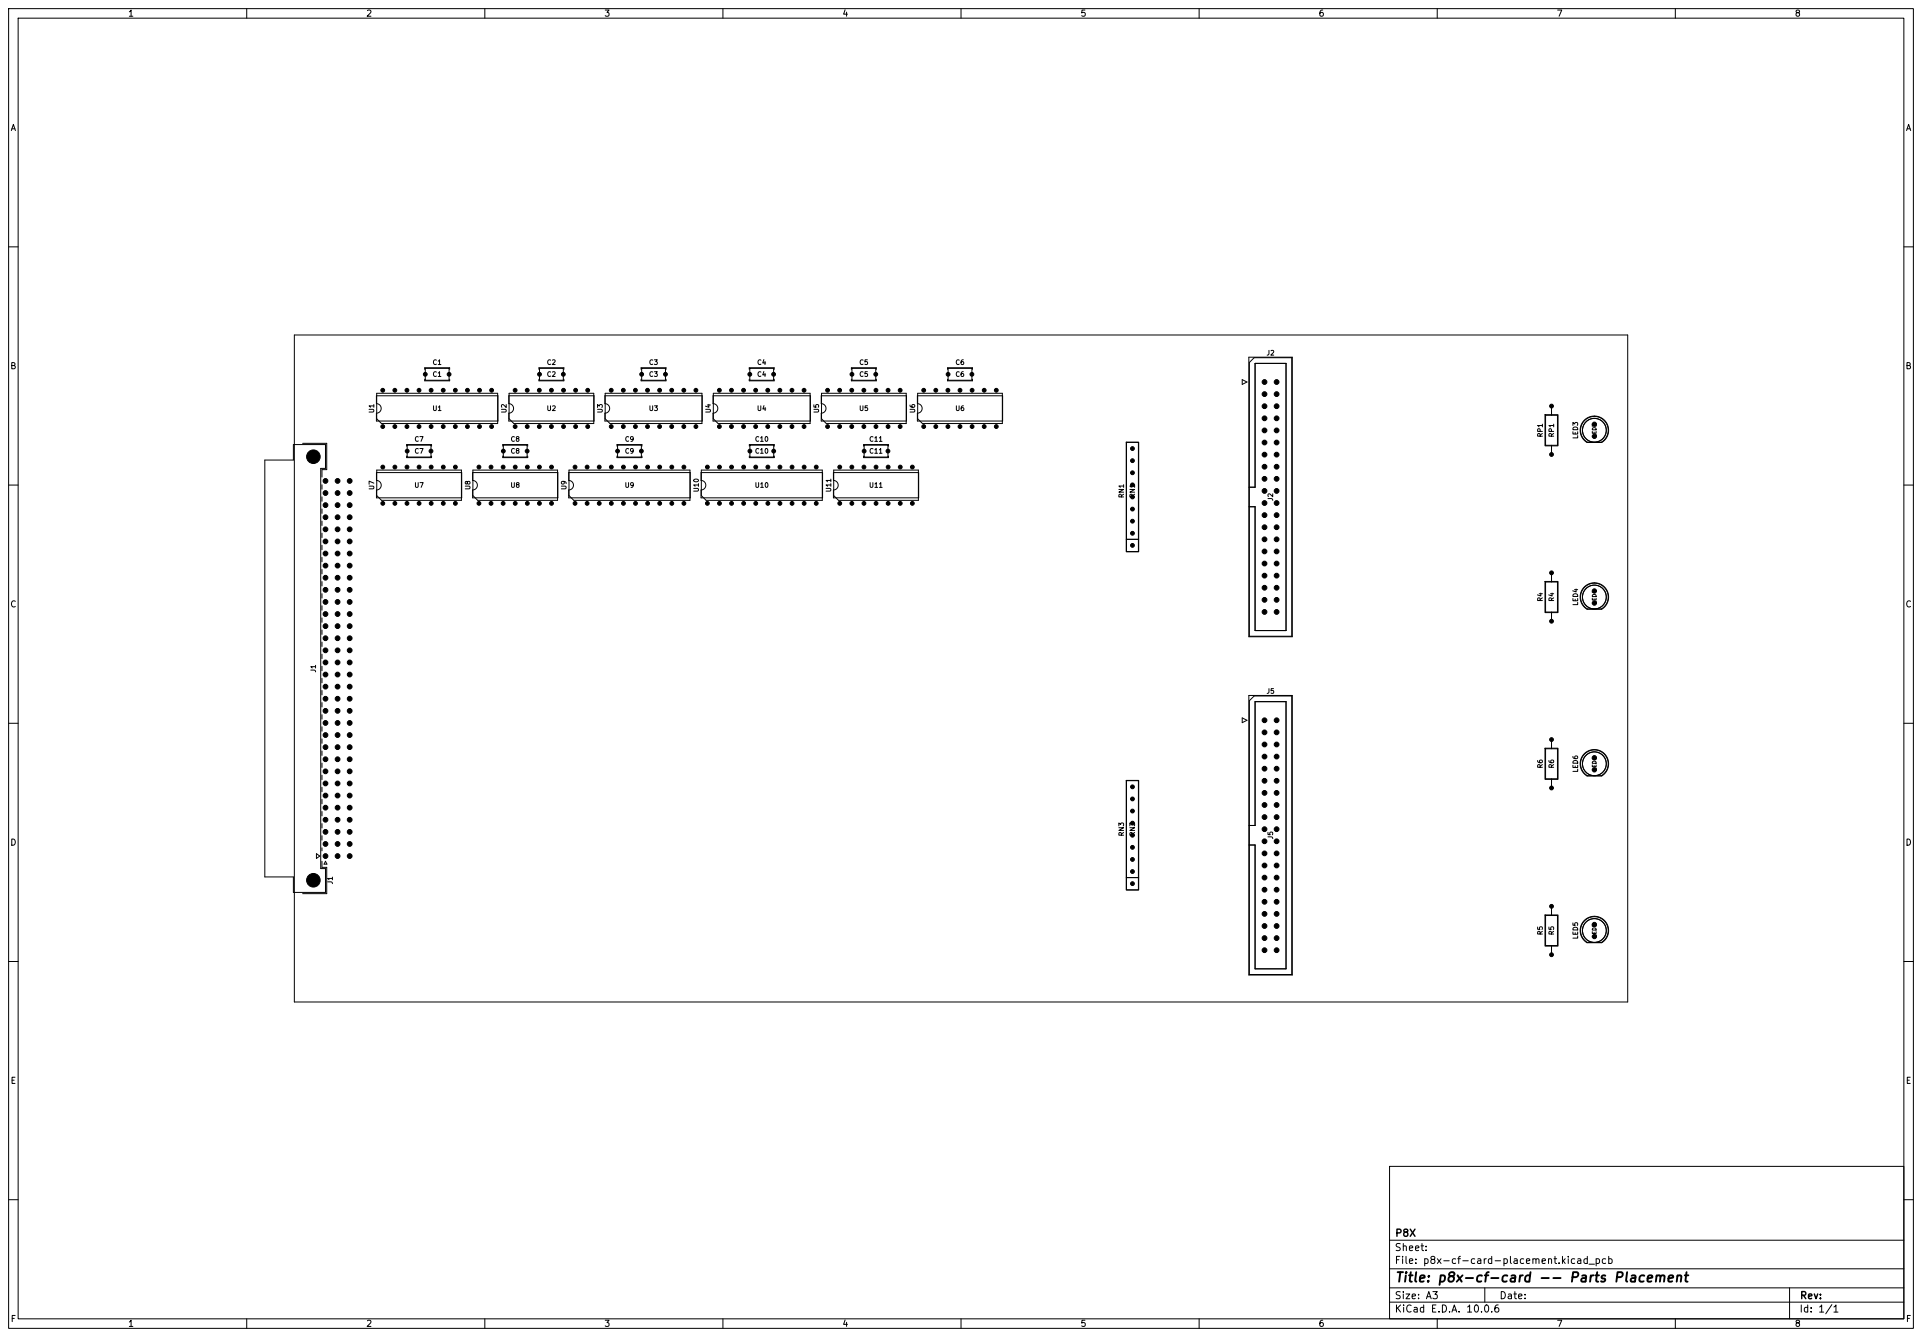
[picture p35: page 1]

Sheet:
File: p8x-cf-card-placement.kicad_pcb
Title: p8x-cf-card -- Parts Placement

Size: A3 | Rev: | F Date:
KiCad E.D.A. 10.0.6 | Id: 1/1
