ksr/p8x/hardware/io-card/kicad/p8x-io-card-placement.pdf

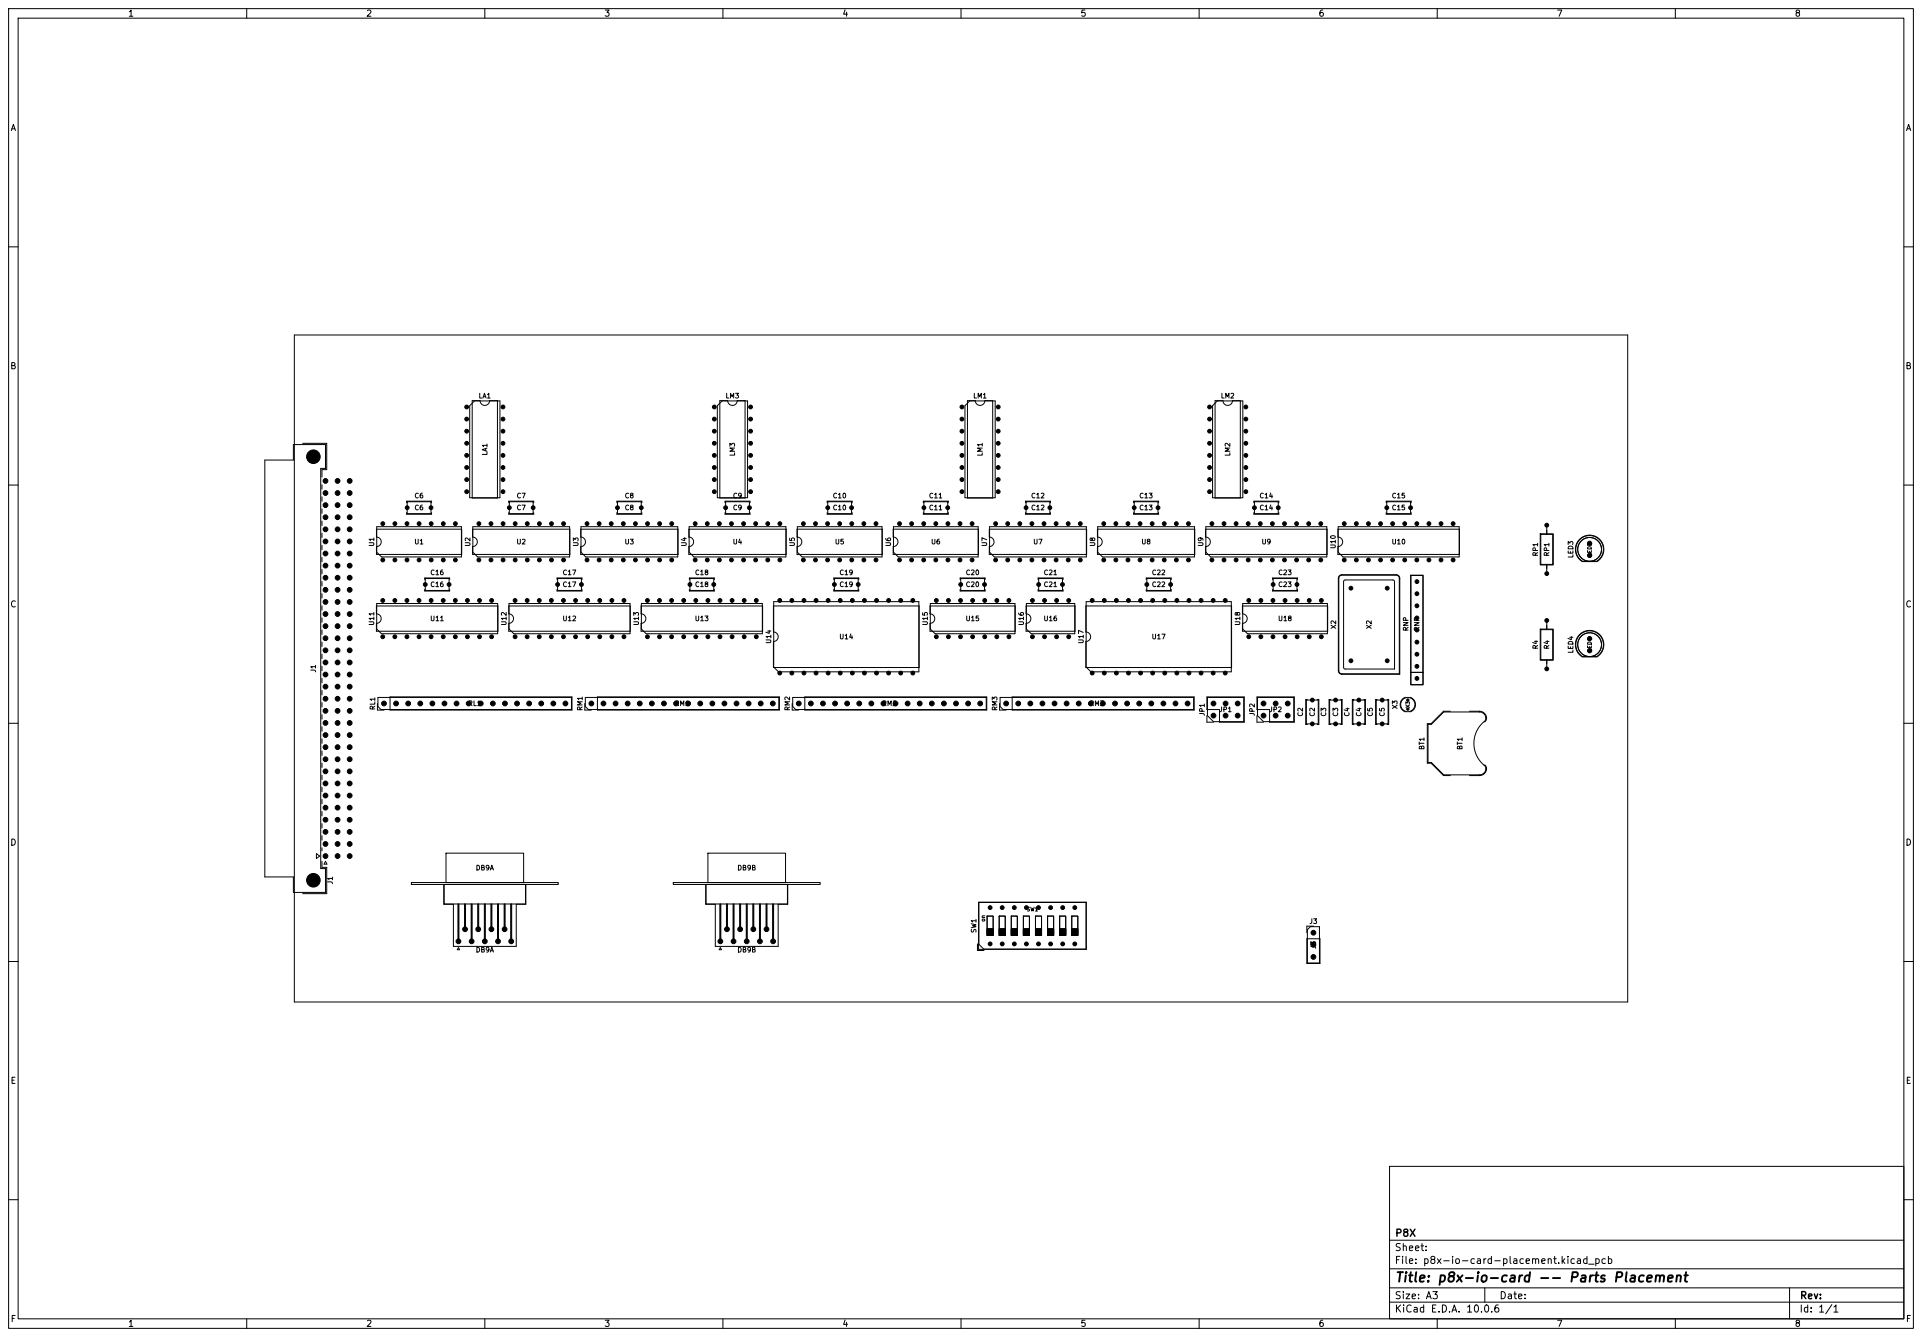
[picture p36: page 1]

Sheet:
File: p8x-io-card-placement.kicad_pcb
Title: p8x-io-card -- Parts Placement

Size: A3 | Rev: | F Date:
KiCad E.D.A. 10.0.6 | Id: 1/1
