ksr/p8x/hardware/ps2-card/kicad/p8x-ps2-card-placement.pdf

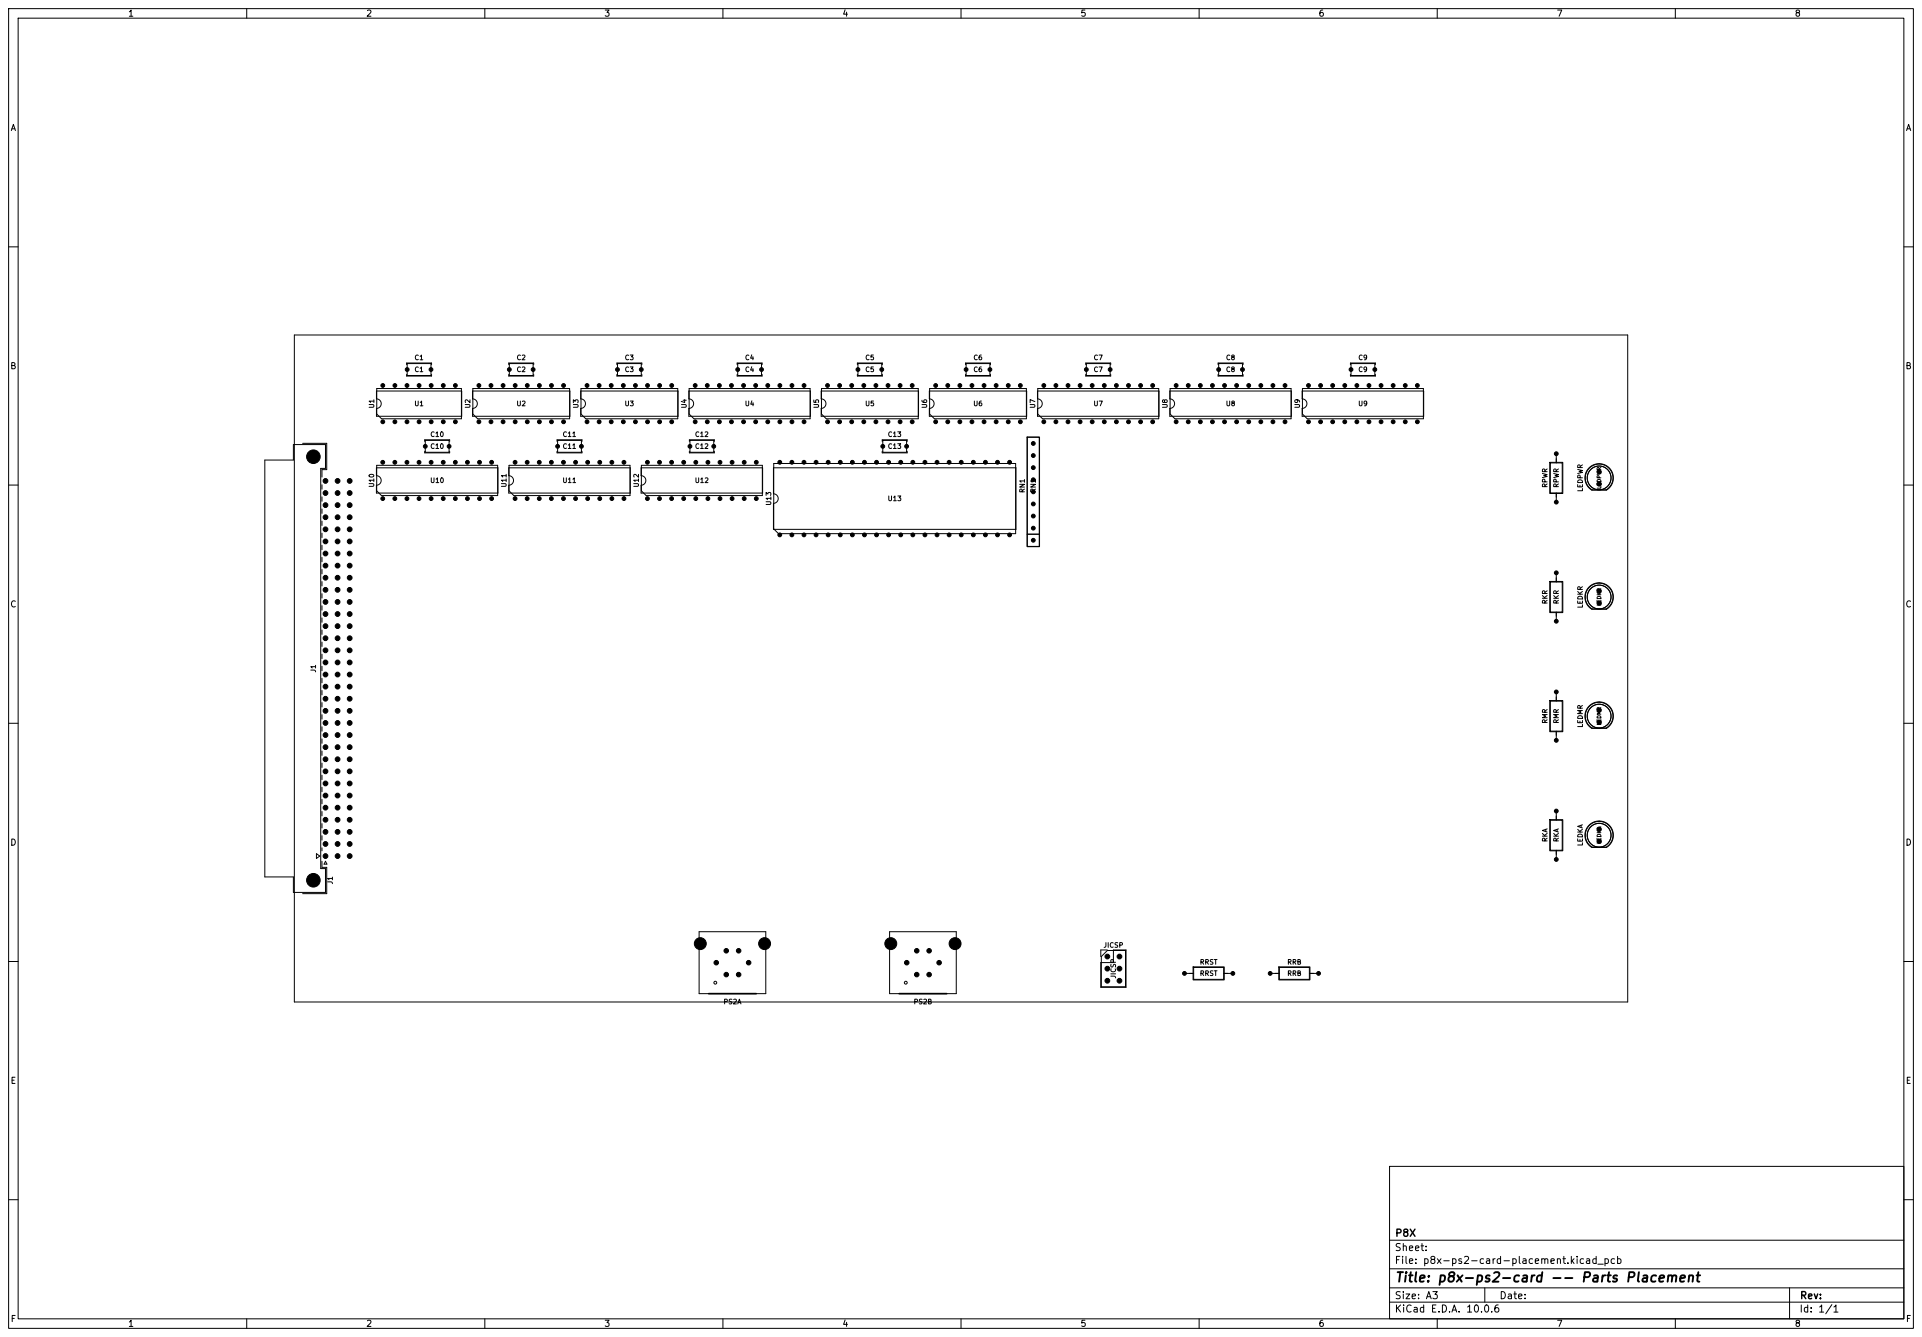
[picture p37: page 1]

Sheet:
File: p8x-ps2-card-placement.kicad_pcb
Title: p8x-ps2-card -- Parts Placement

Size: A3 | Rev: | F Date:
KiCad E.D.A. 10.0.6 | Id: 1/1
