ksr/p8x/hardware/backplane/kicad/p8x-backplane-placement.pdf

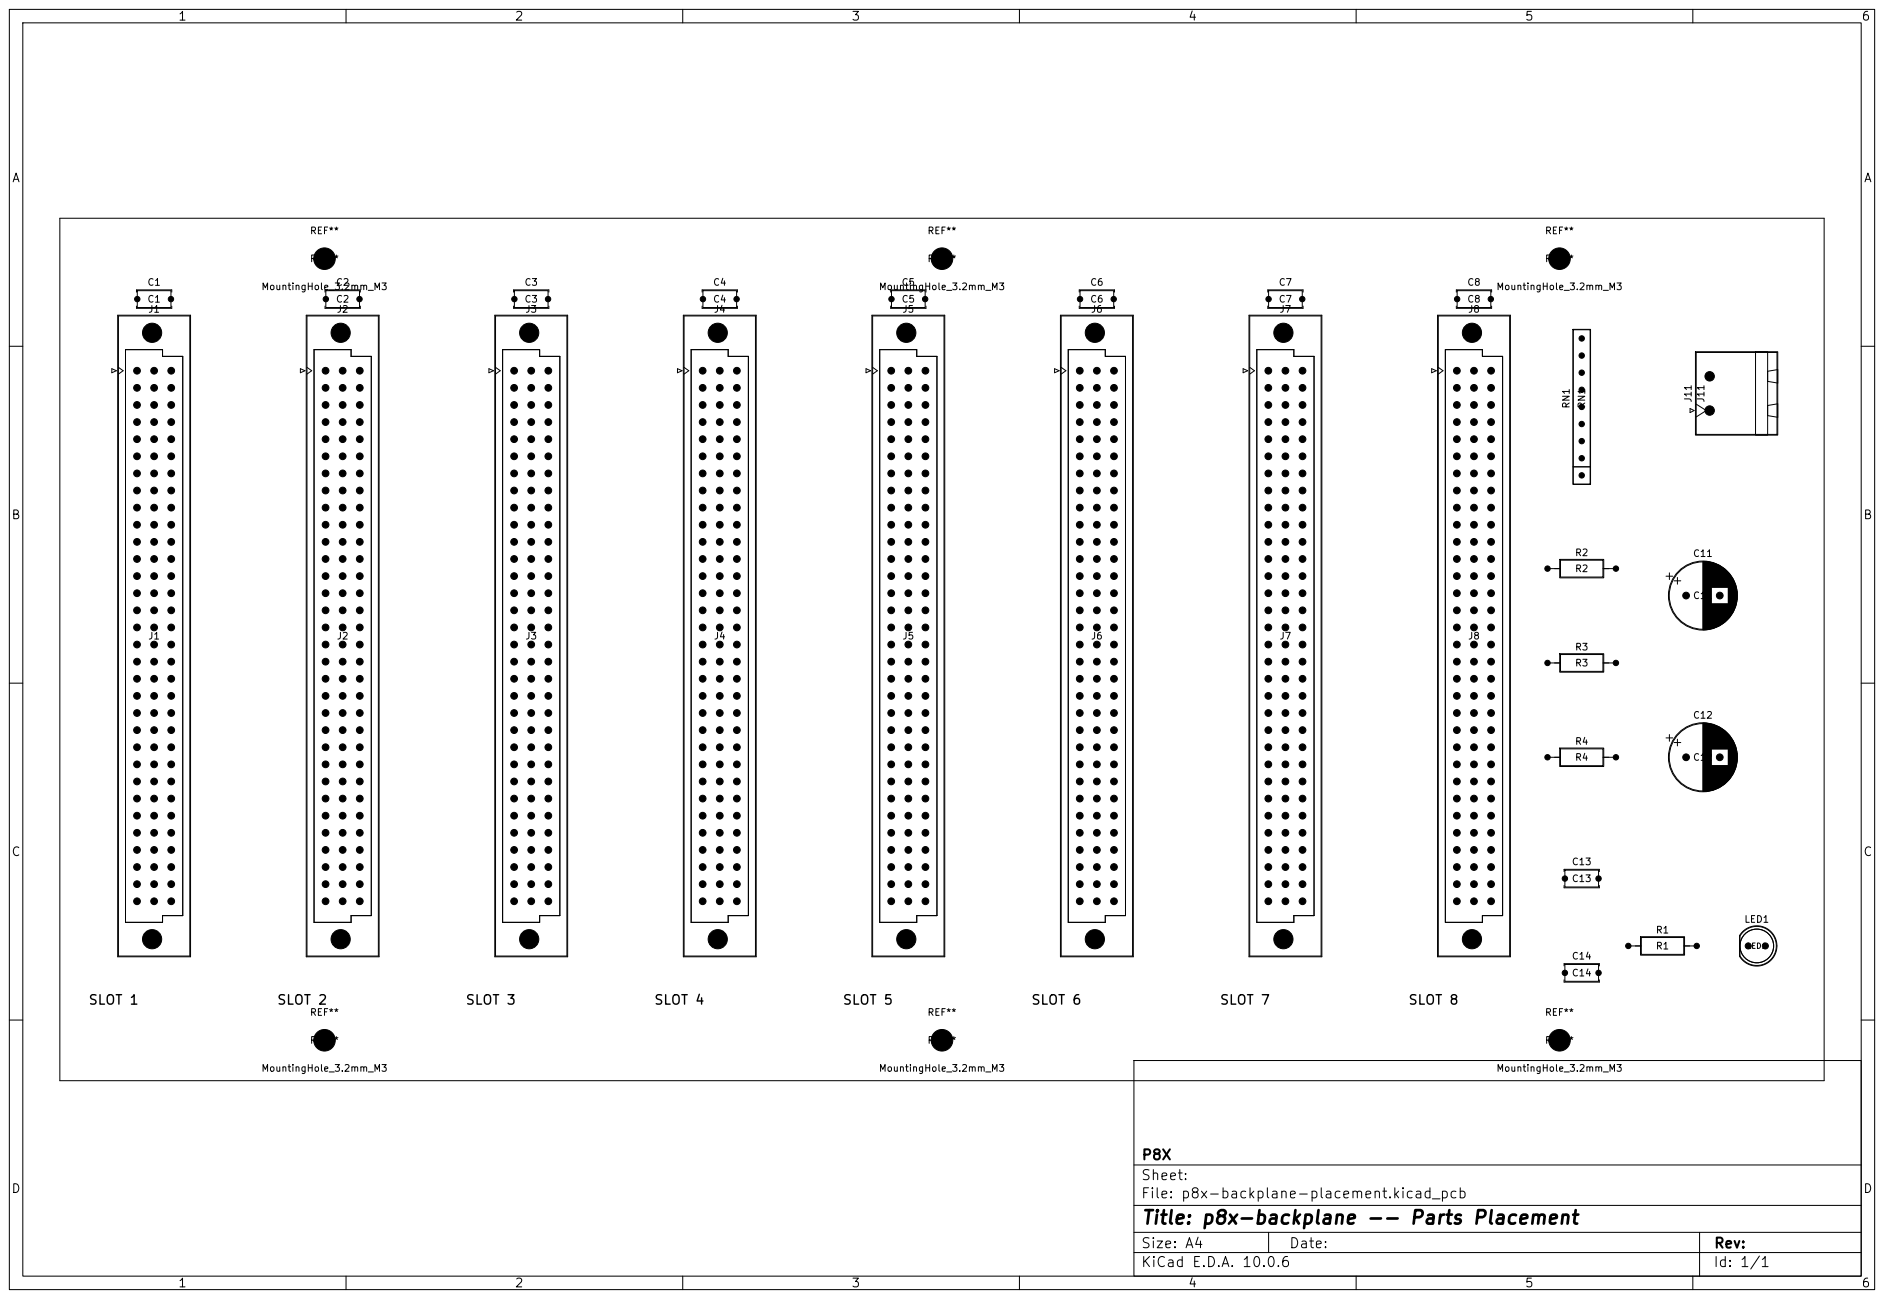
[picture p38: page 1]

Sheet:
File: p8x-backplane-placement.kicad_pcb
Title: p8x-backplane -- Parts Placement

Size: A4 | Rev:
KiCad E.D.A. 10.0.6 | Id: 1/1
