ksr/p8x/hardware/bustest-card/kicad/p8x-bustest-card-placement.pdf

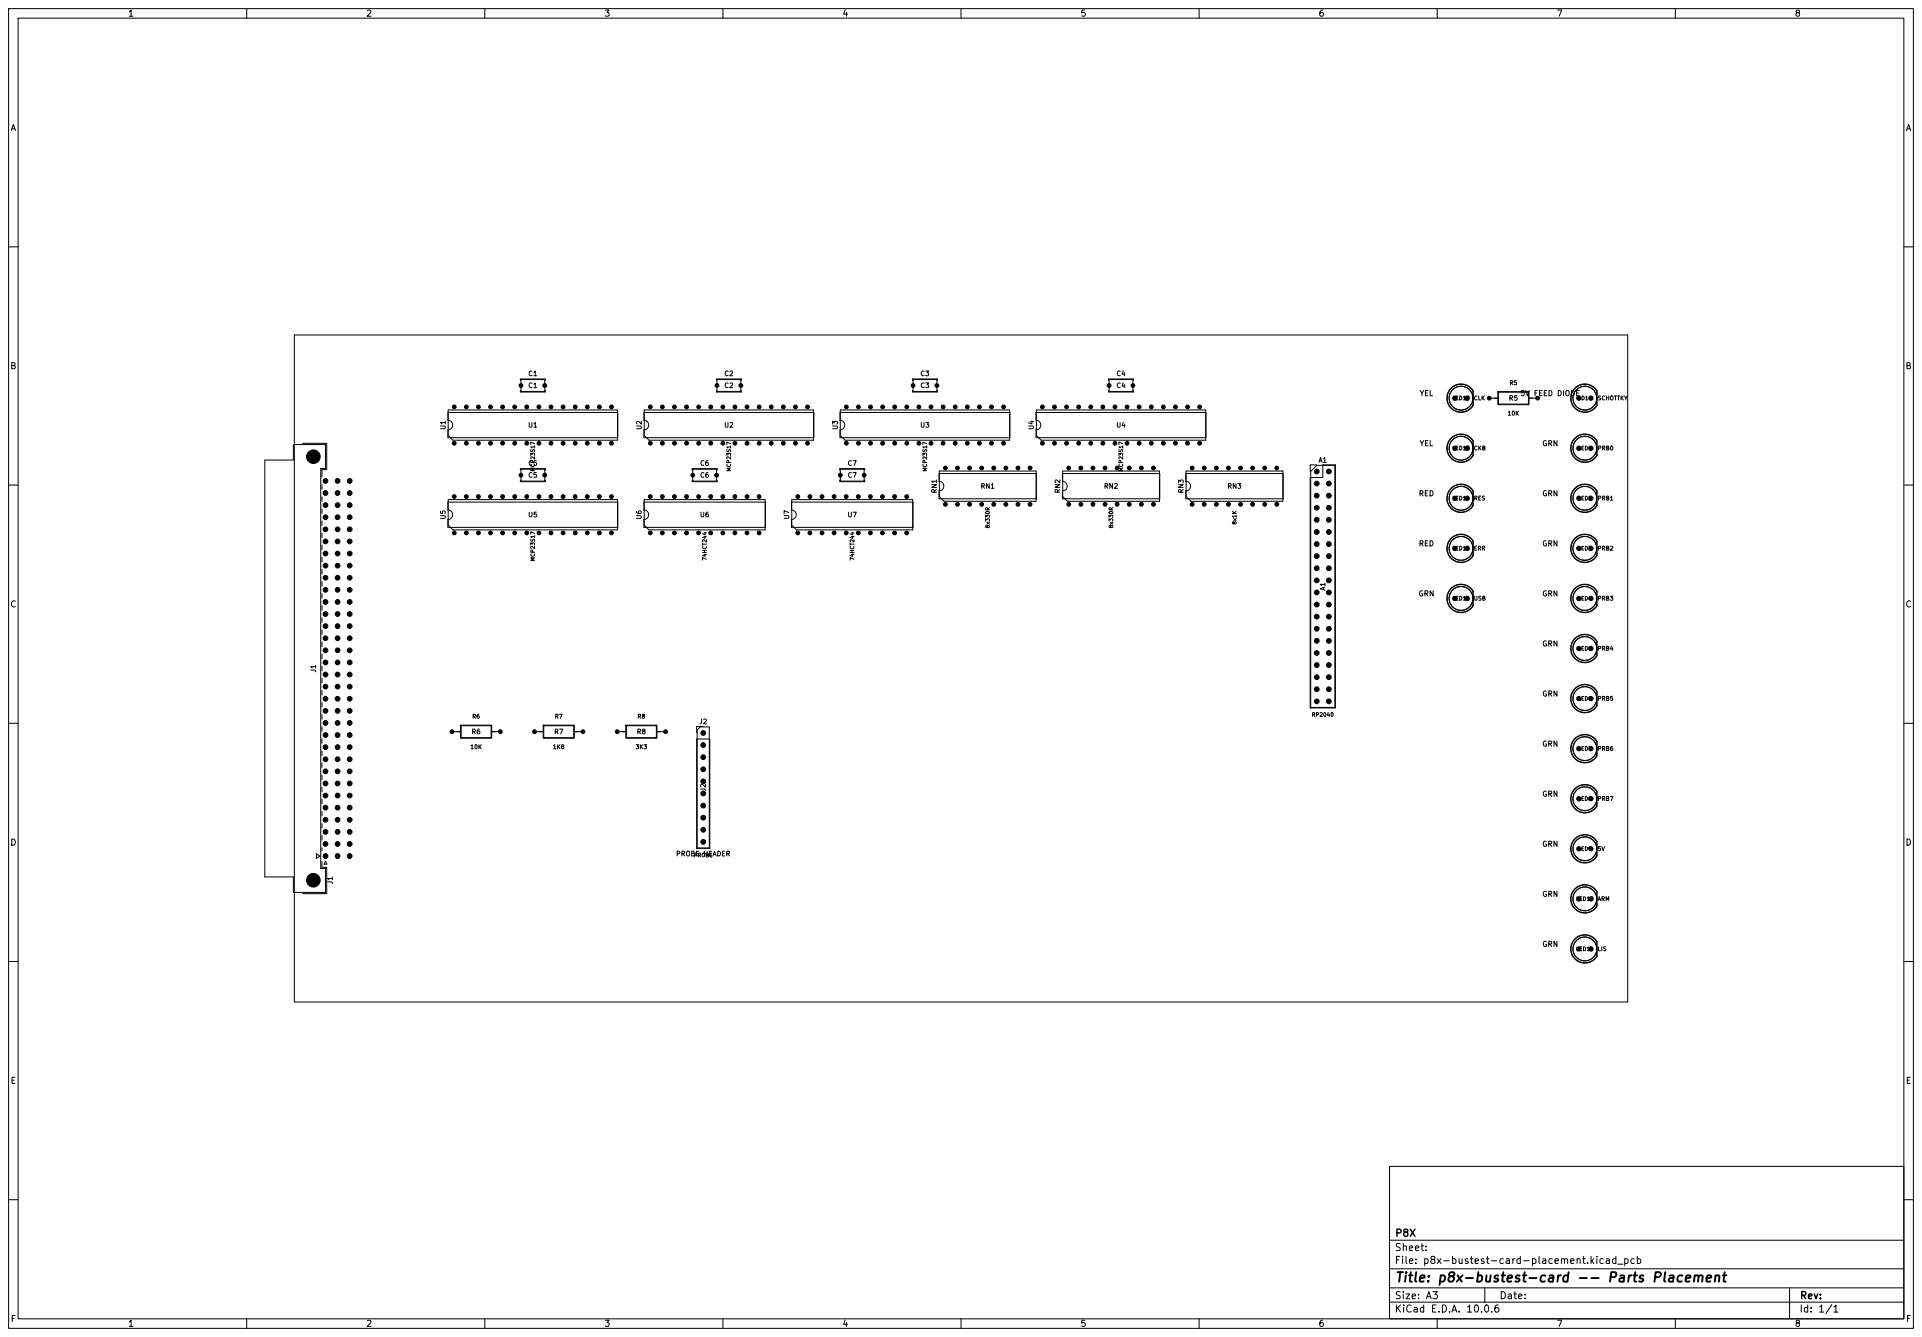
[picture p39: page 1]

Sheet:
File: p8x-bustest-card-placement.kicad_pcb
Title: p8x-bustest-card -- Parts Placement

Size: A3 | Rev: | F Date:
KiCad E.D.A. 10.0.6 | Id: 1/1
