ksr/p8x/hardware/alu-card/kicad/p8x-alu-card-placement.pdf

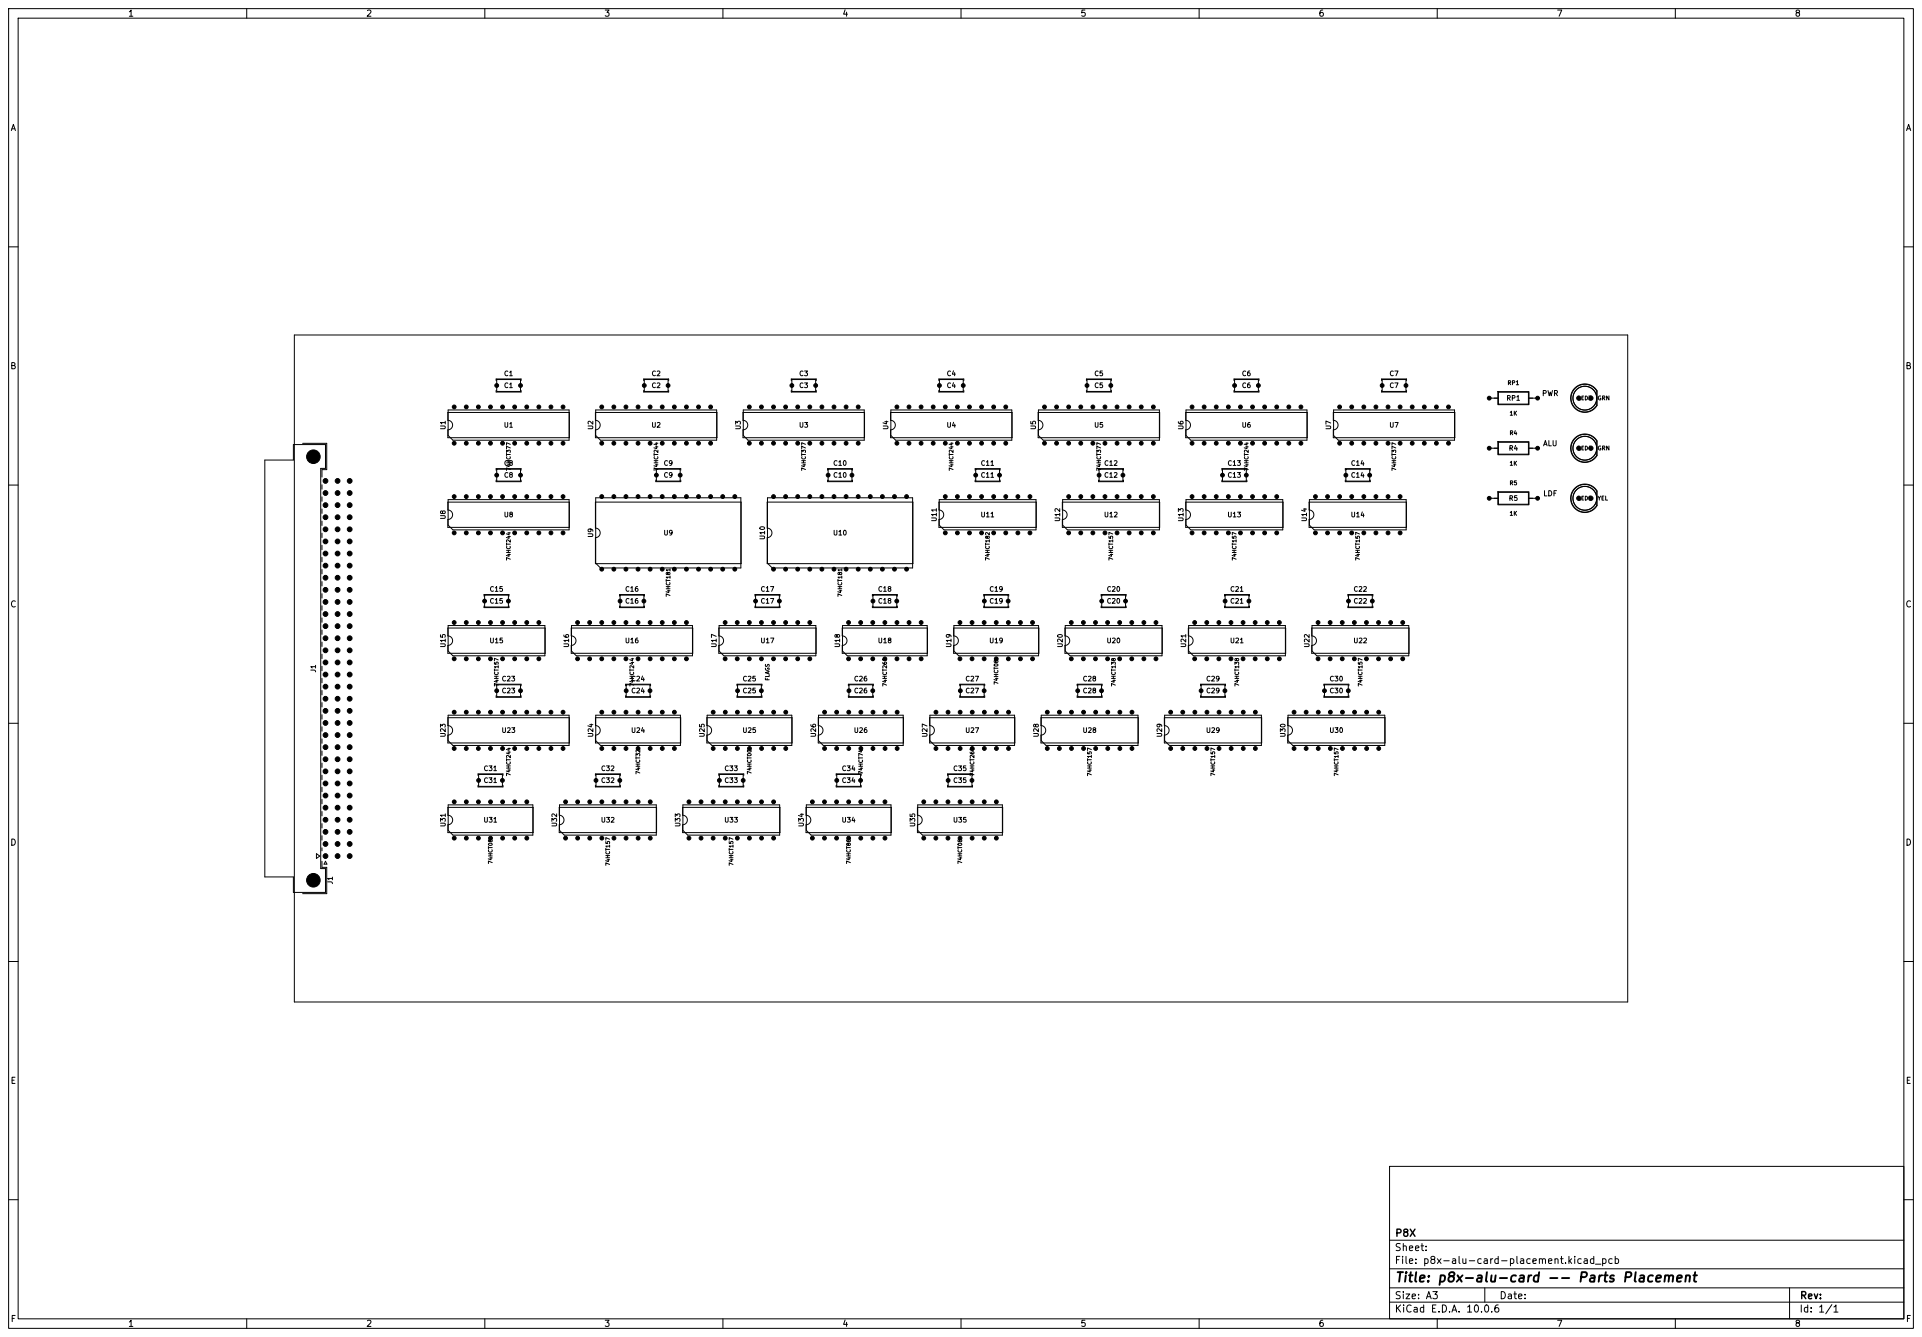
[picture p40: page 1]

Sheet:
File: p8x-alu-card-placement.kicad_pcb
Title: p8x-alu-card -- Parts Placement

Size: A3 | Rev: | F Date:
KiCad E.D.A. 10.0.6 | Id: 1/1
