ksr/p8x/hardware/control-card/kicad/p8x-control-card-placement.pdf

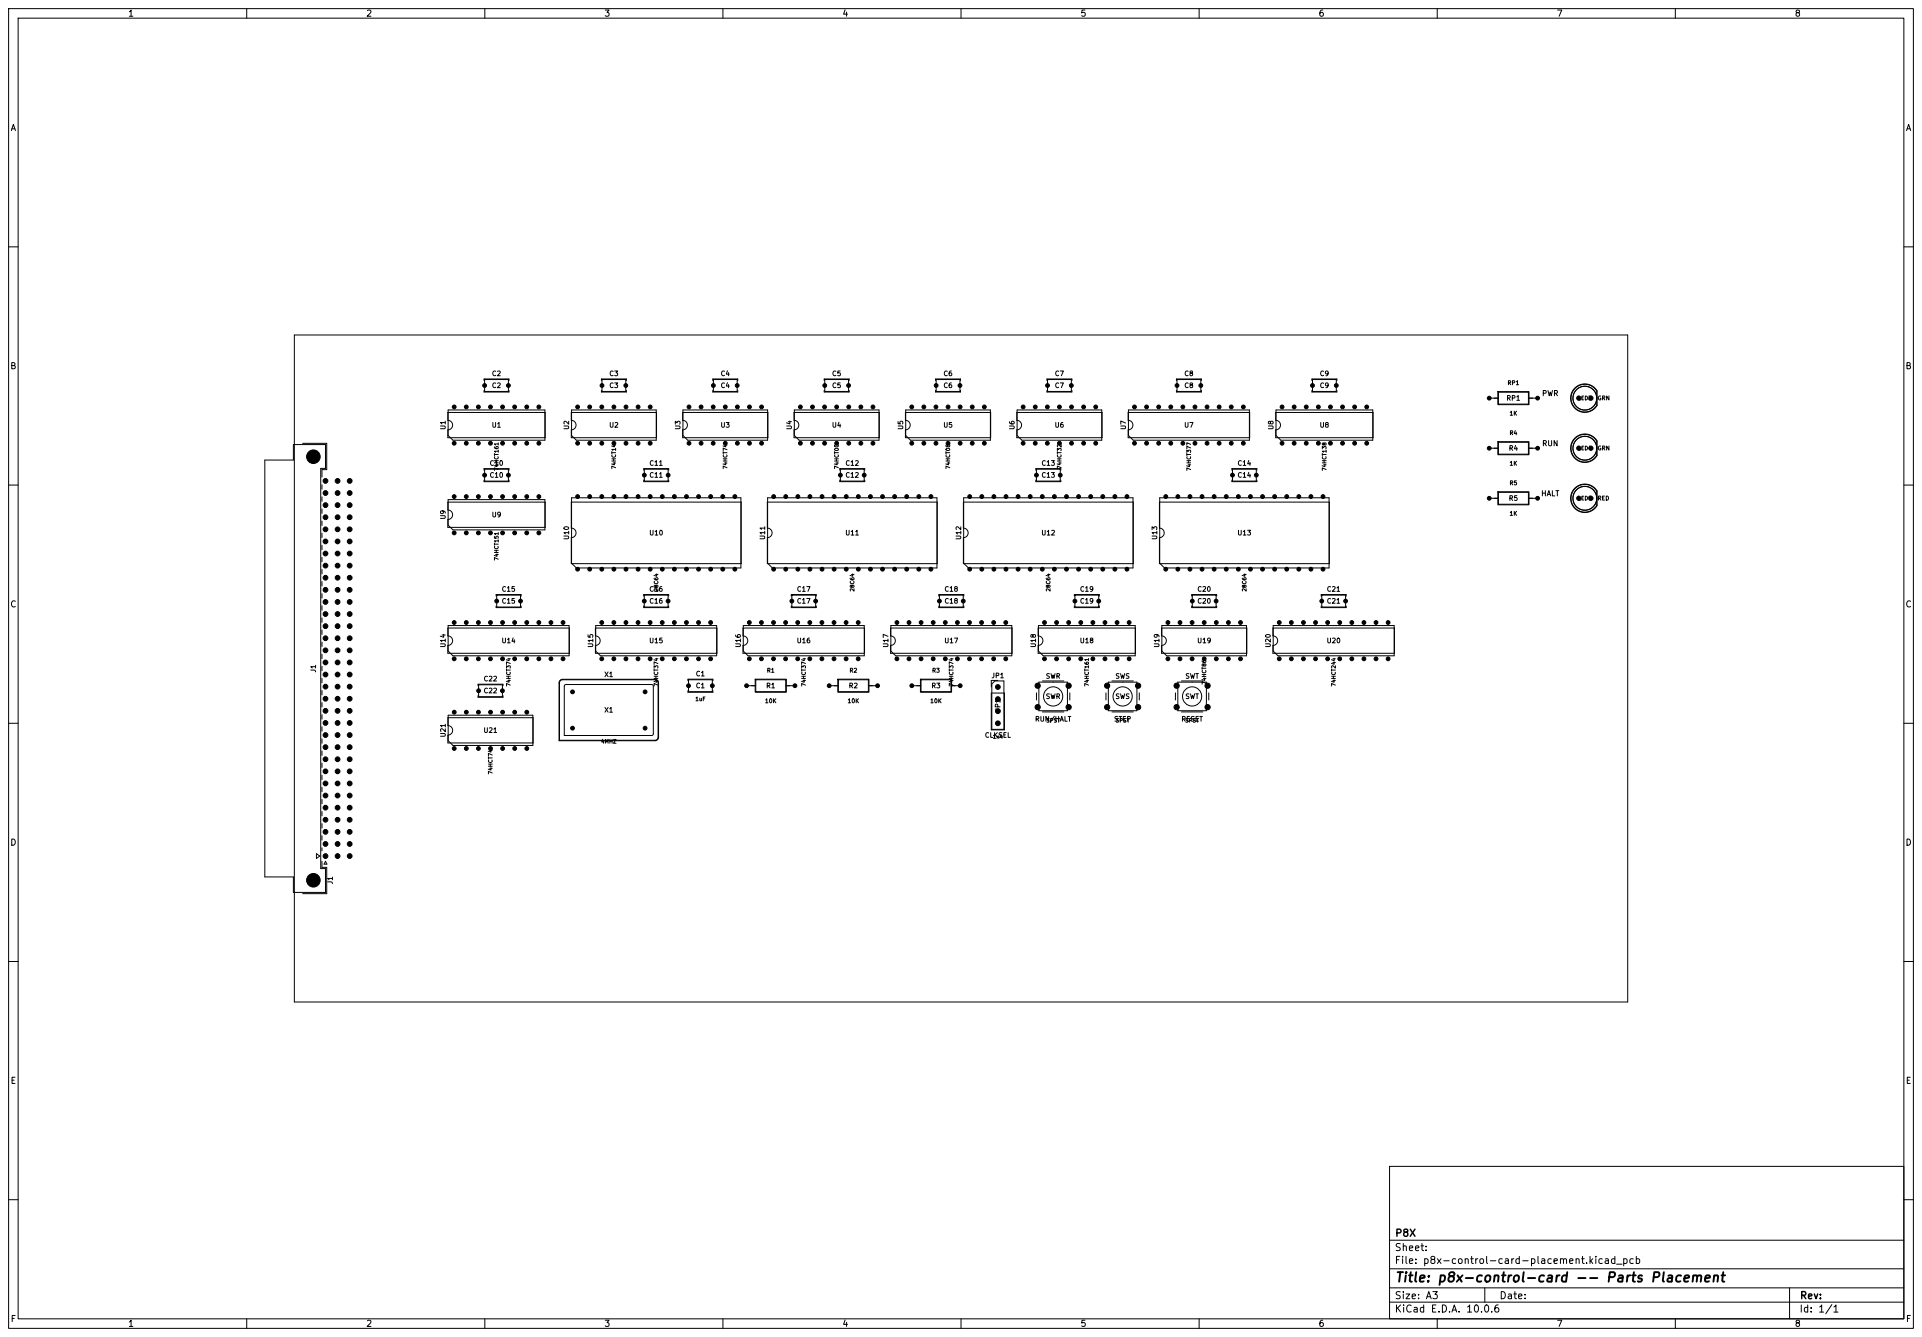
[picture p41: page 1]

Sheet:
File: p8x-control-card-placement.kicad_pcb
Title: p8x-control-card -- Parts Placement

Size: A3 | Rev: | F Date:
KiCad E.D.A. 10.0.6 | Id: 1/1
