ksr/p8x/hardware/memory-card/kicad/p8x-memory-card-placement.pdf

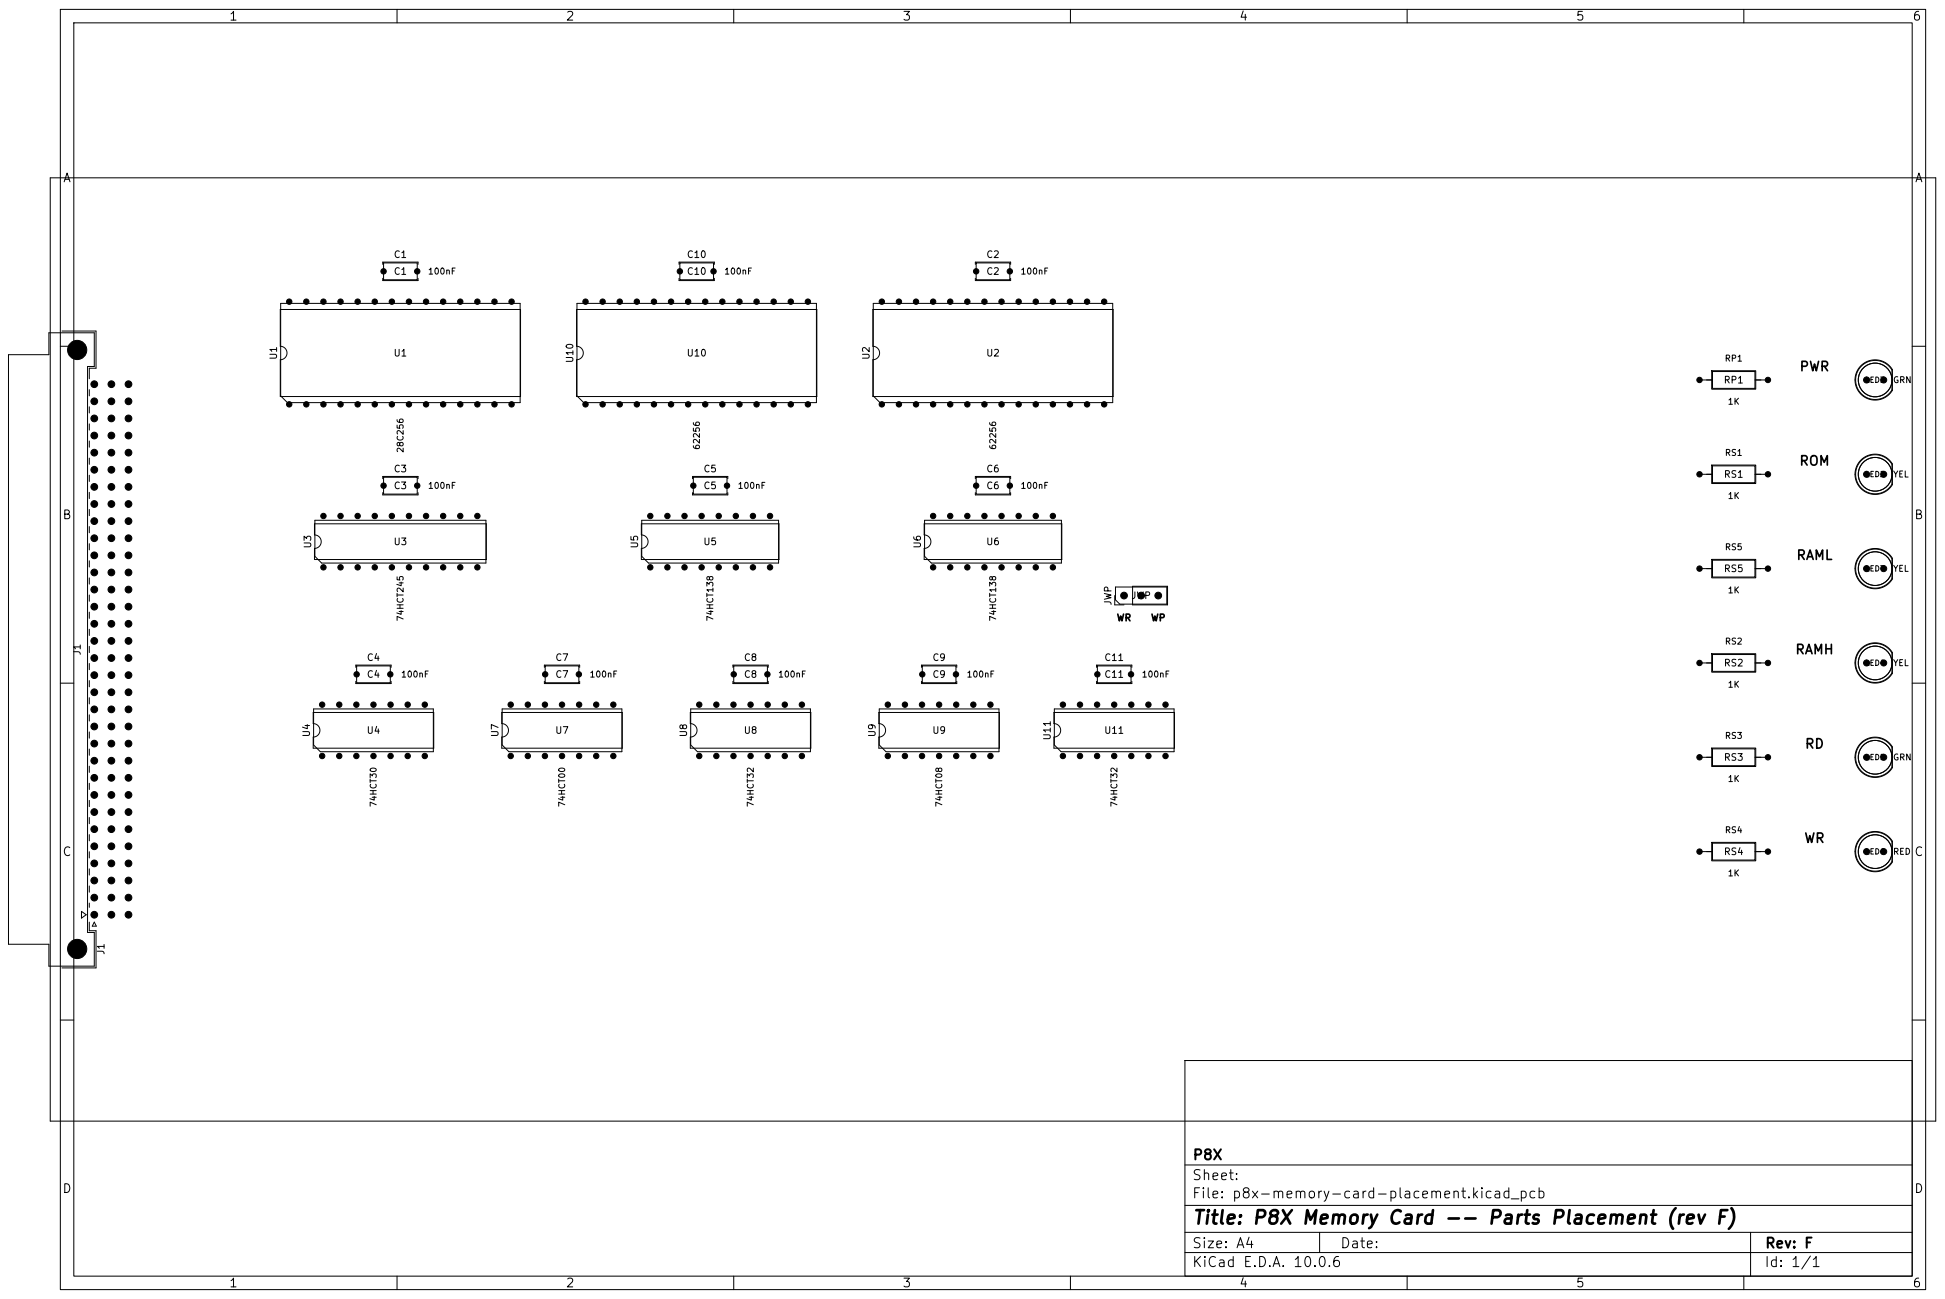
[picture p42: page 1]

Sheet:
File: p8x-memory-card-placement.kicad_pcb
Title: P8X Memory Card -- Parts Placement (rev F)

Size: A4 | Rev: F
KiCad E.D.A. 10.0.6 | Id: 1/1
