ksr/p8x/hardware/regbank-card/kicad/p8x-regbank-card-placement.pdf

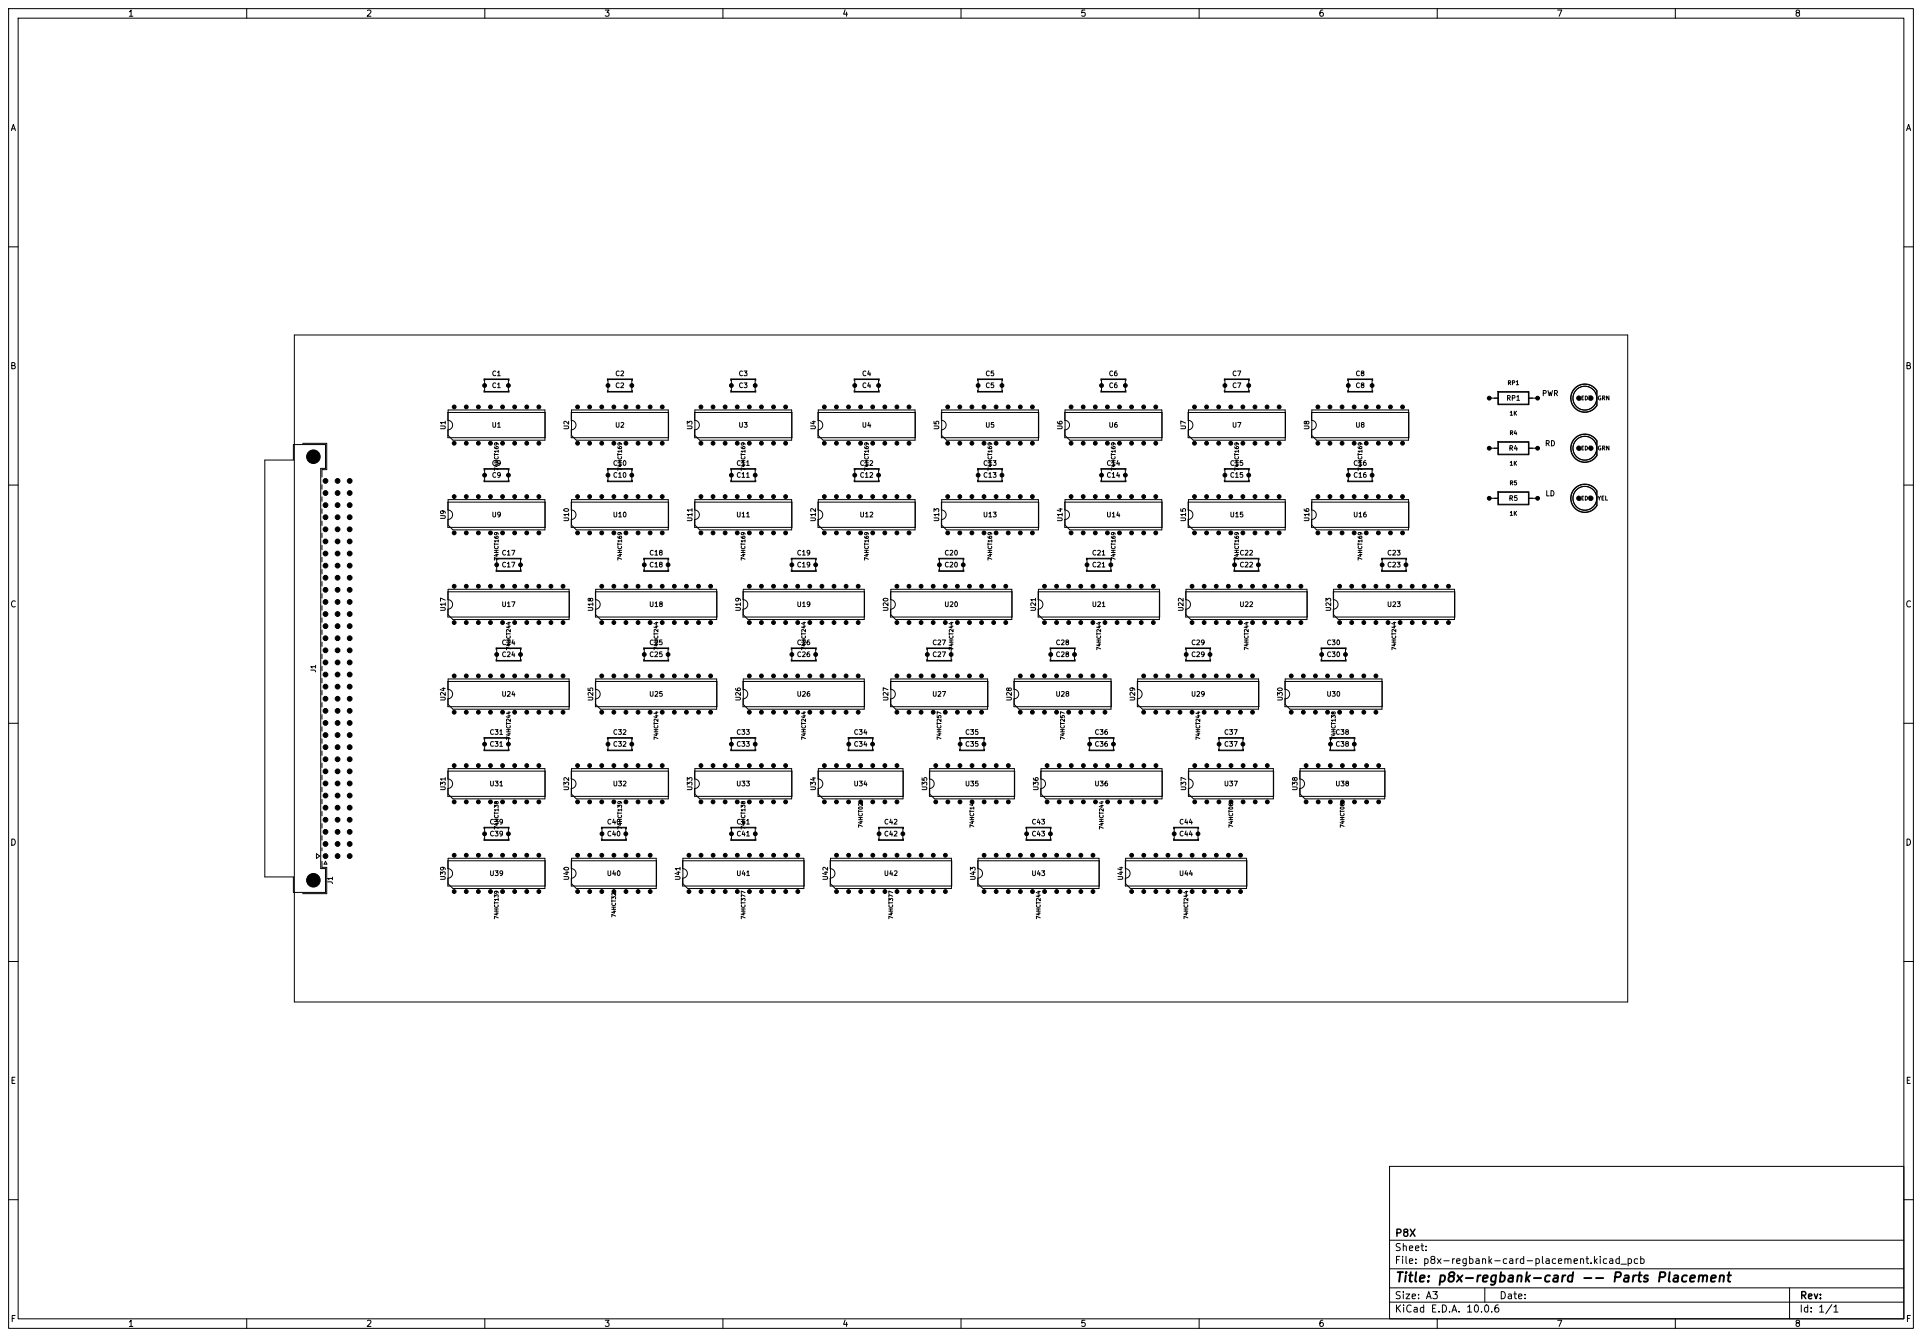
[picture p43: page 1]

Sheet:
File: p8x-regbank-card-placement.kicad_pcb
Title: p8x-regbank-card -- Parts Placement

Size: A3 | Rev: | F Date:
KiCad E.D.A. 10.0.6 | Id: 1/1
