ksr/p8x/hardware/led-card/kicad/p8x-led-card-placement.pdf

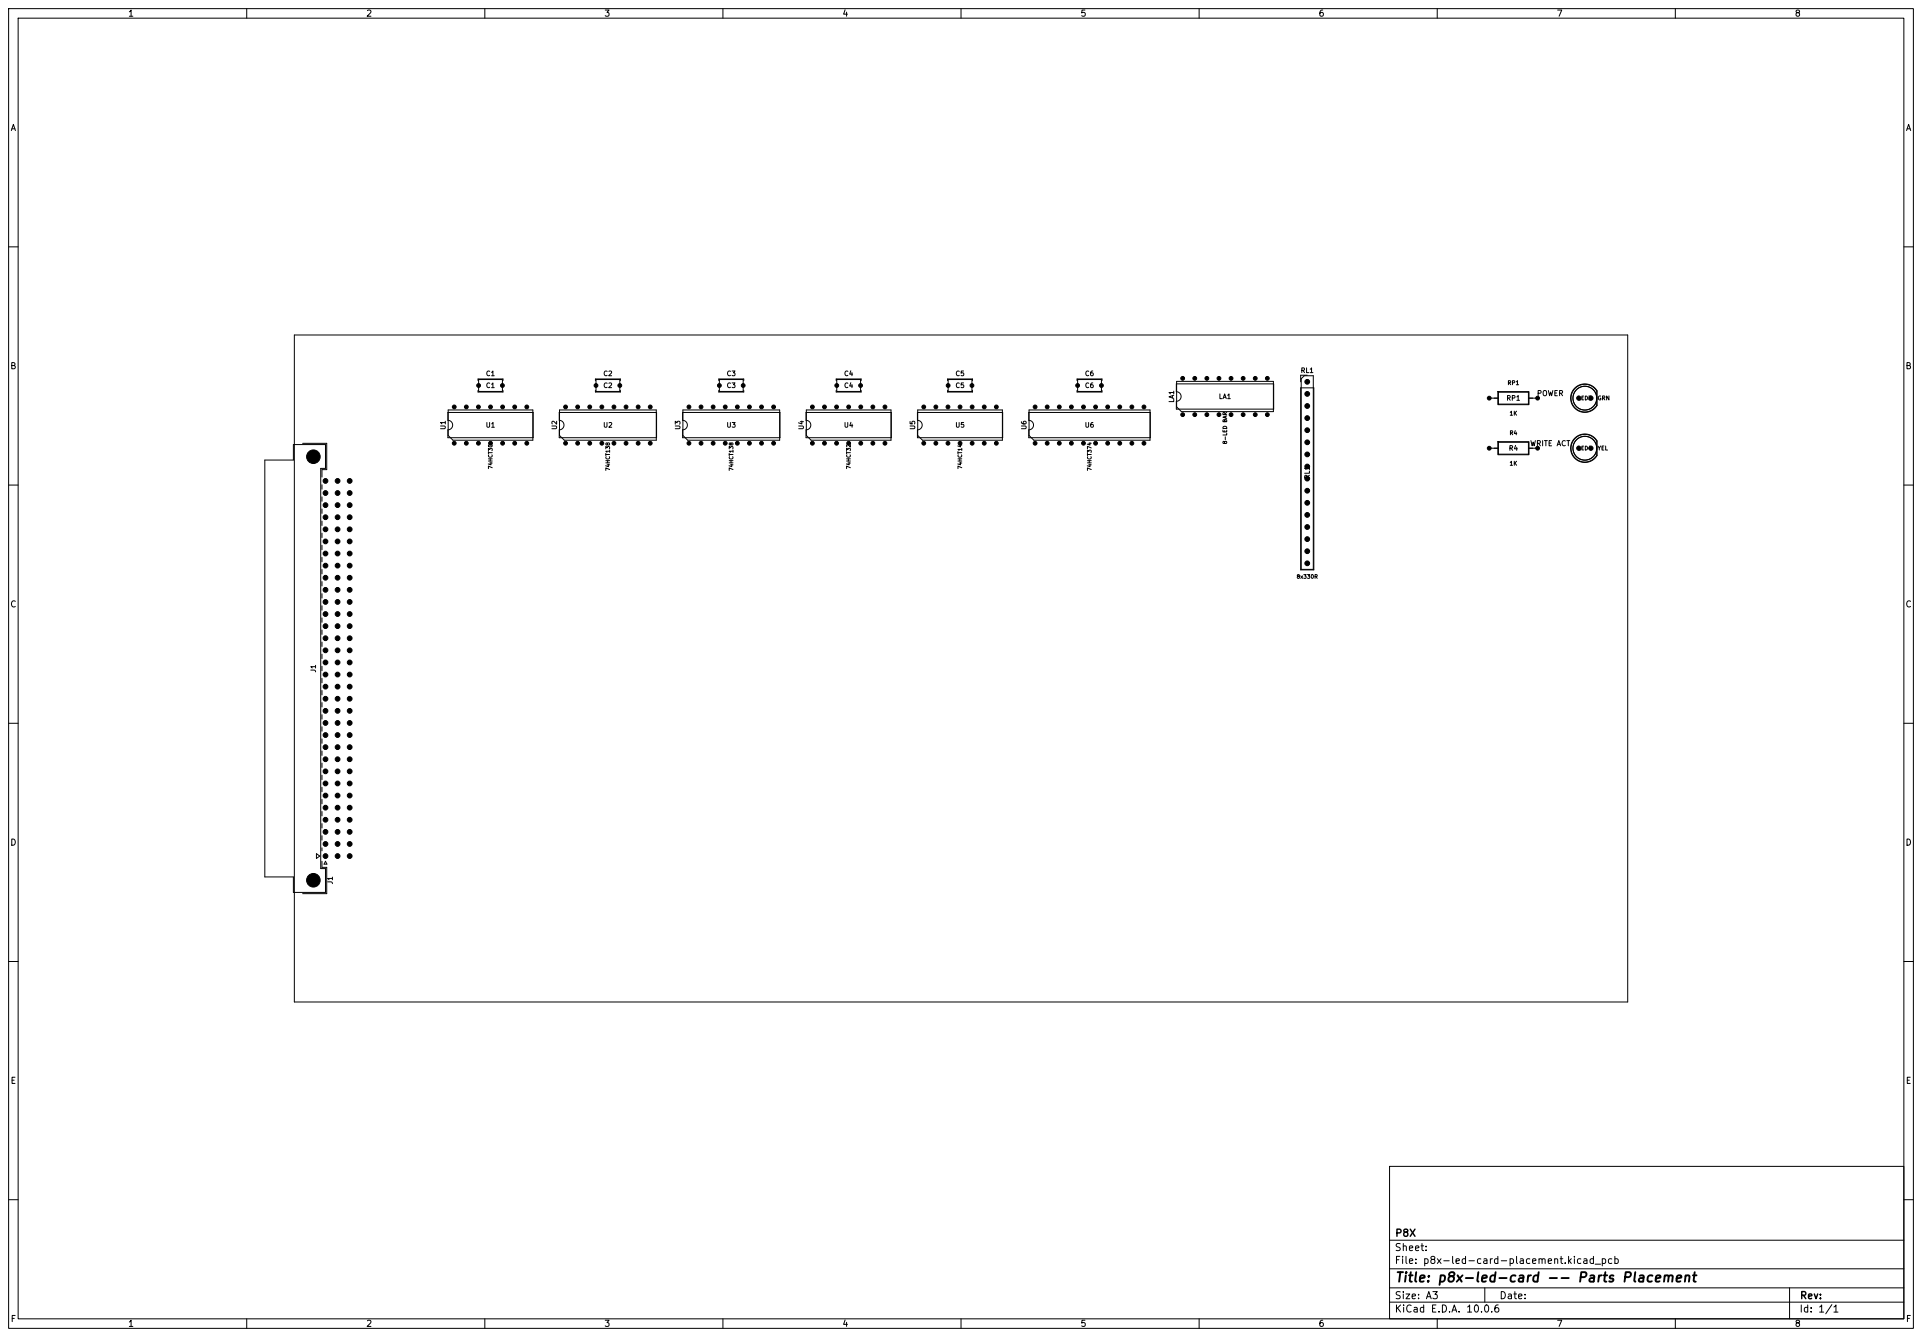
[picture p44: page 1]

Sheet:
File: p8x-led-card-placement.kicad_pcb
Title: p8x-led-card -- Parts Placement

Size: A3 | Rev: | F Date:
KiCad E.D.A. 10.0.6 | Id: 1/1
