ksr/p8x/hardware/xor-trial/kicad/xor_trial_sch.pdf

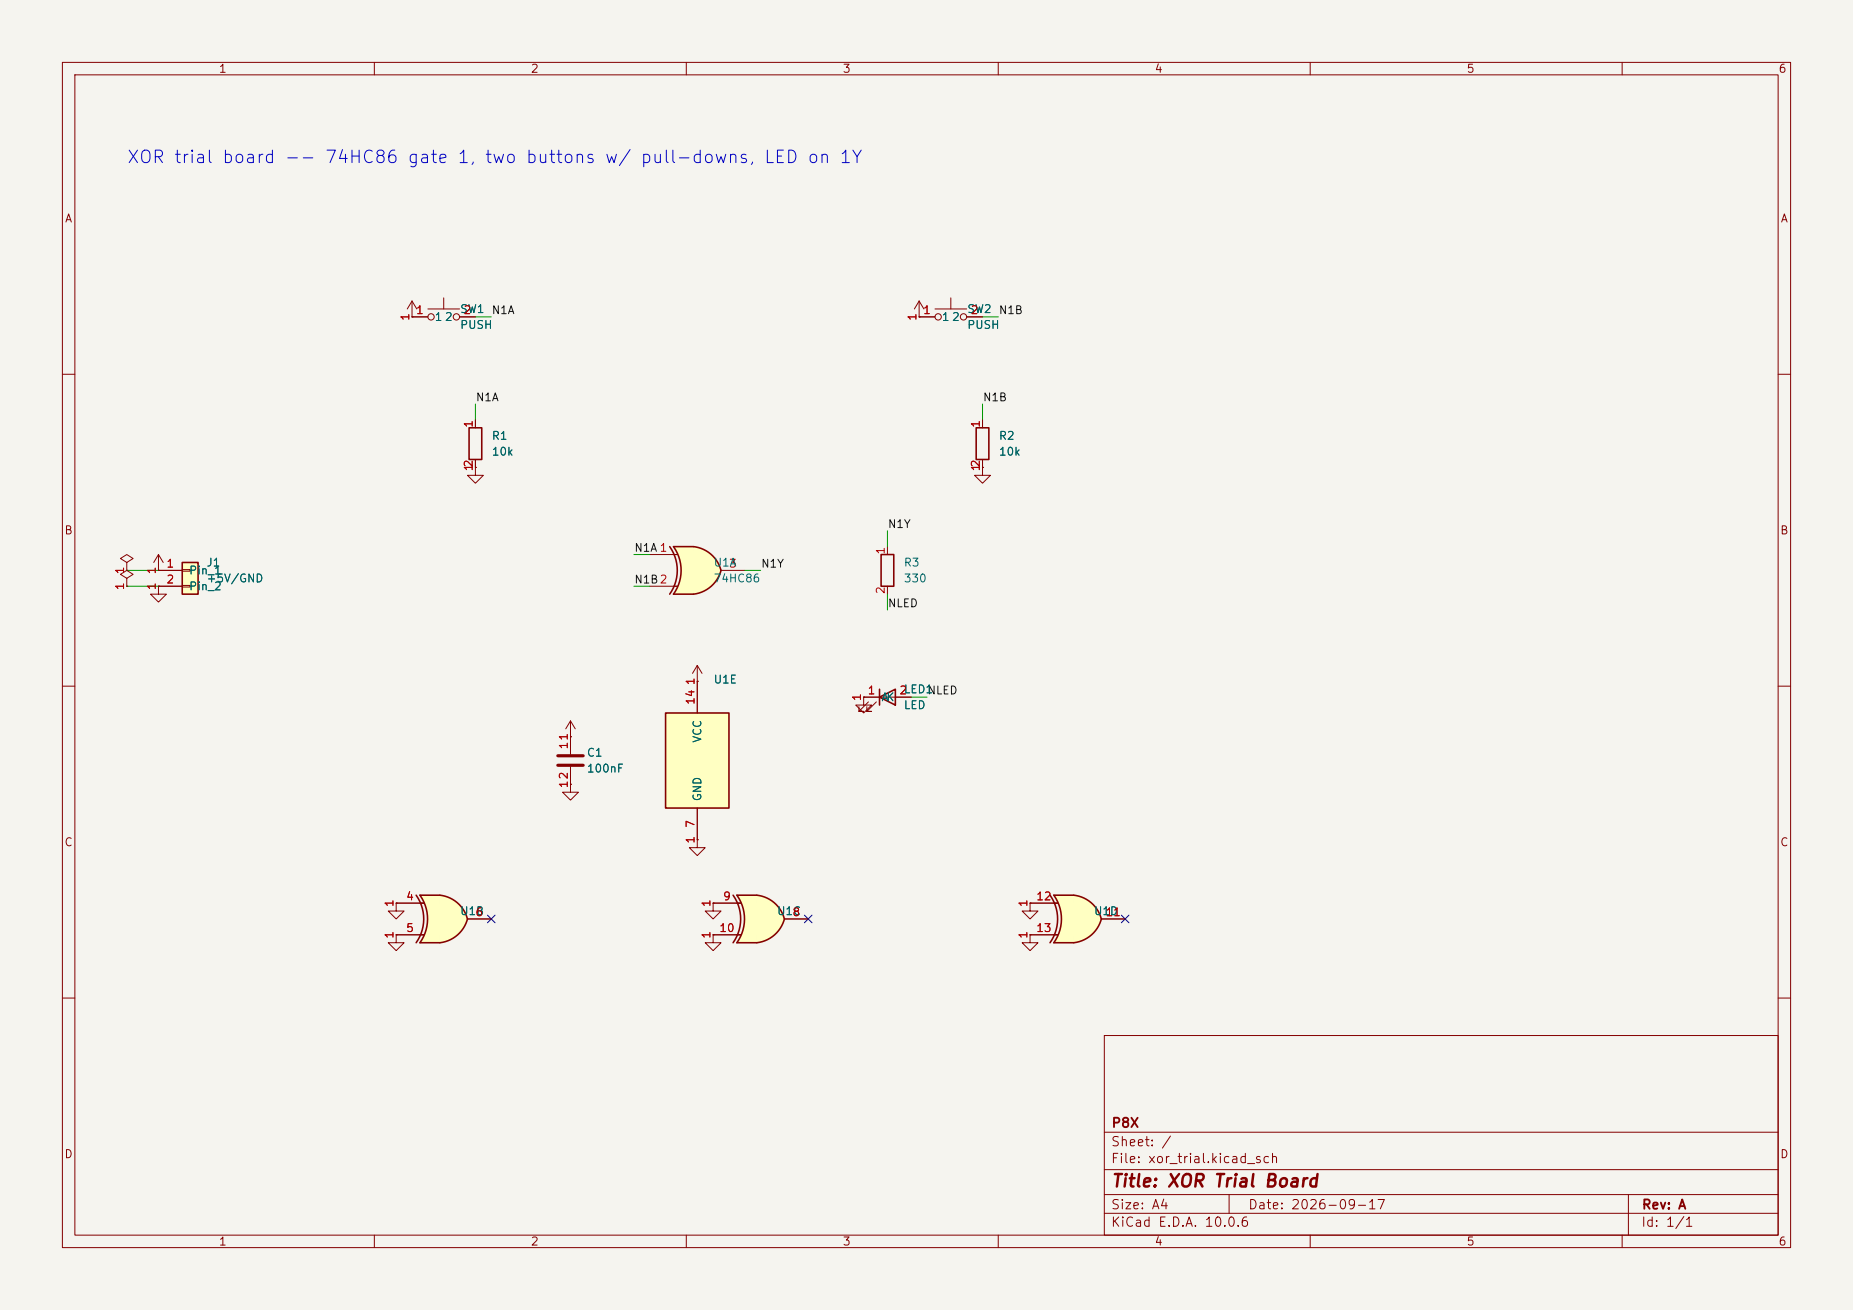
[picture p45: page 1]

1 N1A N1A N1B N1Y N1Y NLED N1B NLED N1B N1A XOR trial board -- 74HC86 gate 1, two buttons w/ pull-downs, LED on 1Y

Size: A4 | Rev: A
KiCad E.D.A. 10.0.6 | Id: 1/1
