ksr/p8x/hardware/parked/peripheral-card/kicad/p8x-peripheral-card-placement.pdf

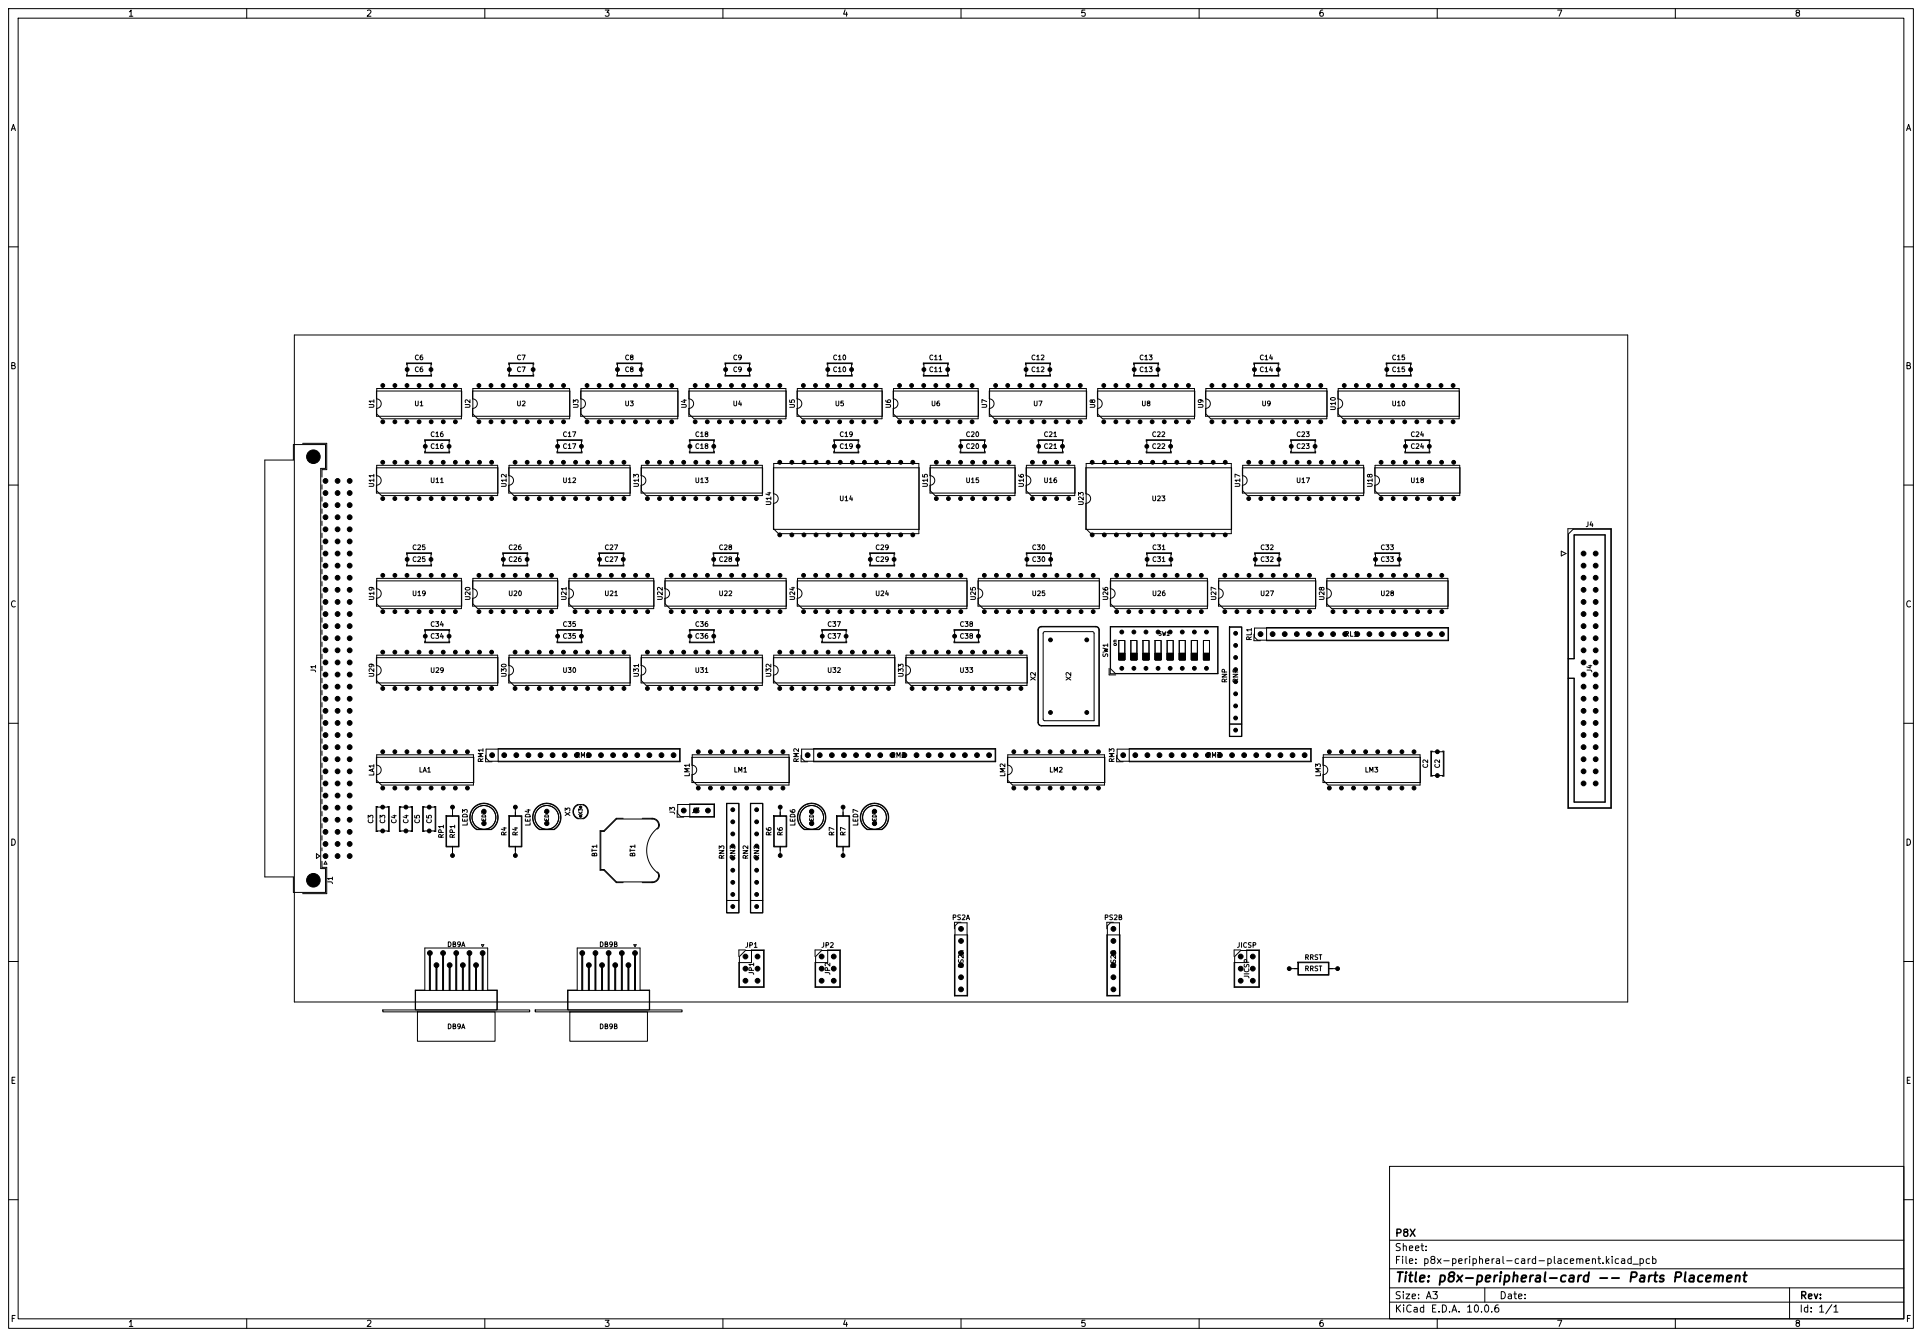
[picture p46: page 1]

Sheet:
File: p8x-peripheral-card-placement.kicad_pcb
Title: p8x-peripheral-card -- Parts Placement

Size: A3 | Rev: | F Date:
KiCad E.D.A. 10.0.6 | Id: 1/1
