ksr/p8x/hardware/arduino-scratch/arduino-scratch-a.brd

## EAGLE design hardware/arduino-scratch/arduino-scratch-a.brd (2026-07-22)

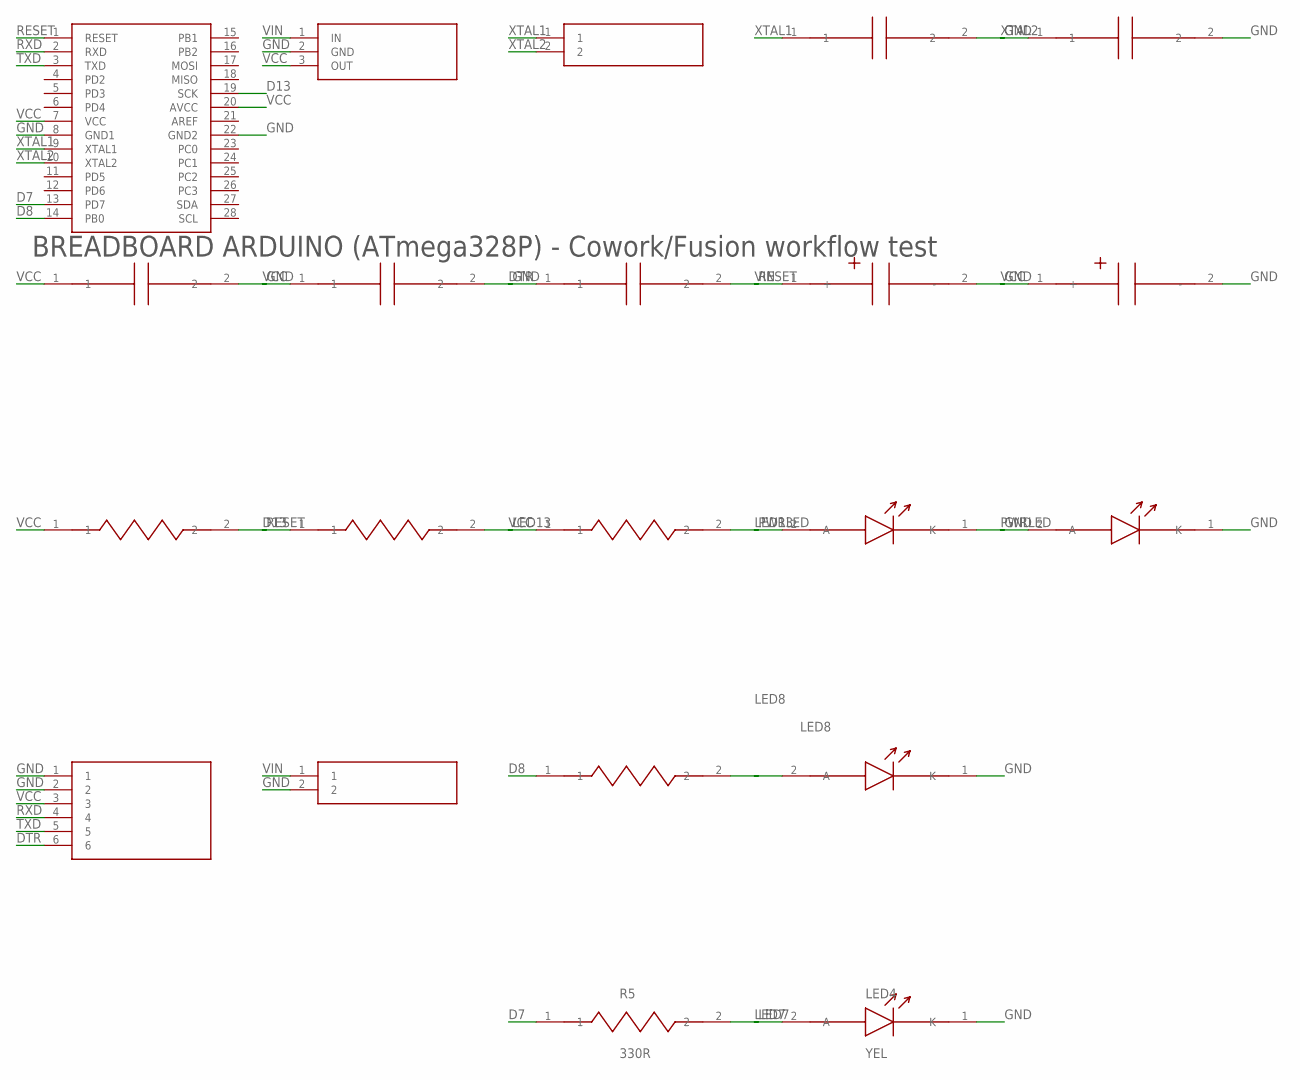
[picture p81: schematic arduino-scratch-a.sch]

Parts:
C1, C2: 22P; C_DISC
C3, C4, C5: 100N; C_DISC
C6, C7: 10U; CP_RADIAL
J1: FTDI; HDR6
J2: 7-12V DC; HDR2
LED1, LED3, LED4: YEL; LED5
LED2: GRN; LED5
R1: 10K; R_AXIAL
R2, R4, R5: 330R; R_AXIAL
R3: 1K; R_AXIAL
U1: ATMEGA328P-PU; DIP28N
U2: 7805; TO220
Y1: 16MHZ; HC49

Connections:
D7: R5.1, U1.13 (PD7)
D8: R4.1, U1.14 (PB0)
D13: R2.1, U1.19 (SCK)
DTR: C5.1, J1.6
GND: C1.2, C2.2, C3.2, C4.2, C6.2 (-), C7.2 (-), J1.1, J1.2, J2.2, LED1.1 (K), LED2.1 (K), LED3.1 (K), LED4.1 (K), U1.8 (GND1), U1.22 (GND2), U2.2 (GND)
LED7: LED4.2 (A), R5.2
LED8: LED3.2 (A), R4.2
LED13: LED1.2 (A), R2.2
PWRLED: LED2.2 (A), R3.2
RESET: C5.2, R1.2, U1.1 (RESET)
RXD: J1.4, U1.2 (RXD)
TXD: J1.5, U1.3 (TXD)
VCC: C3.1, C4.1, C7.1 (+), J1.3, R1.1, R3.1, U1.7 (VCC), U1.20 (AVCC), U2.3 (OUT)
VIN: C6.1 (+), J2.1, U2.1 (IN)
XTAL1: C1.1, U1.9 (XTAL1), Y1.1
XTAL2: C2.1, U1.10 (XTAL2), Y1.2

Notes on the sheet:
BREADBOARD ARDUINO (ATmega328P) - Cowork/Fusion workflow test

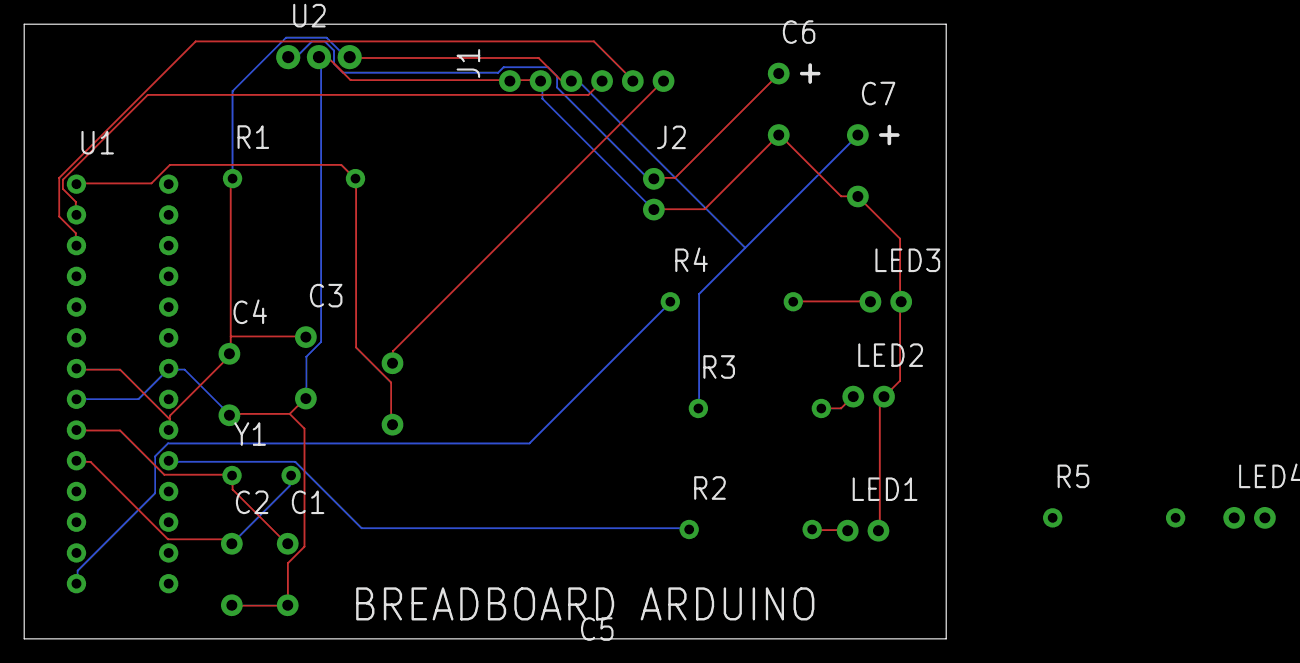
[picture p82: board arduino-scratch-a.brd from above]

Board: 4 copper layers, 76.2 x 50.8 mm, 21 parts (0 on the bottom side), 16 nets.
