ksr/p8x/generators/gen_arduino.py

#!/usr/bin/env python3
"""Breadboard-Arduino test board (ATmega328P from scratch) — a Cowork<->Fusion
workflow probe, NOT part of the P8X machine.

Minimal standalone AVR board after the classic "Arduino from scratch" recipe:
ATmega328P-PU + 16 MHz crystal + reset pull-up + a 7805 5 V regulator (with in/out
caps) + a 6-pin FTDI programming/serial header (with the DTR auto-reset cap) + a
pin-13 LED and a power LED. Through-hole only.

Reuses gen_eagle's low-level emitters (write_sch / write_brd / validate) and its
device library, but NOT card() — card() forces a P8X DIN96 edge connector, and
this board has none. Emits Eagle .sch/.brd into hardware/arduino-scratch/, parts
parked off-board (unplaced) with the ratsnest, ready to place + route in Fusion.

    python3 generators/gen_arduino.py
"""
import os, sys
sys.path.insert(0, os.path.dirname(os.path.abspath(__file__)))
import gen_eagle as G

OUTDIR = os.path.join(os.path.dirname(os.path.dirname(os.path.abspath(__file__))),
                      "hardware", "arduino-scratch")

# ---- new footprints (through-hole; (pad, x, y, drill, dia) in mm) --------------
G.PKG["HC49"]  = [("1",0,0,0.8,1.6), ("2",4.88,0,0.8,1.6)]                  # HC-49/U crystal
G.PKG["TO220"] = [("1",0,0,1.0,2.0), ("2",2.54,0,1.0,2.0), ("3",5.08,0,1.0,2.0)]
G.PKG["HDR6"]  = [(str(k+1),0,-2.54*k,0.9,1.8) for k in range(6)]           # 1x6 FTDI
G.PKG["HDR2"]  = [(str(k+1),0,-2.54*k,0.9,1.8) for k in range(2)]           # 1x2 power in

# ---- new devices (pin-name -> pad map) -----------------------------------------
# ATmega328P-PU, 28-pin narrow DIP. Pins named by primary function; pm maps each
# to its physical pad (1..28). L = pads 1..14, R = pads 15..28.
_L = ["RESET","RXD","TXD","PD2","PD3","PD4","VCC","GND1","XTAL1","XTAL2","PD5","PD6","PD7","PB0"]
_R = ["PB1","PB2","MOSI","MISO","SCK","AVCC","AREF","GND2","PC0","PC1","PC2","PC3","SDA","SCL"]
_pm = {n:str(i+1)  for i,n in enumerate(_L)}
_pm.update({n:str(i+15) for i,n in enumerate(_R)})
G.D("ATMEGA328", _L, _R, _pm, "DIP28N")
G.D("XTAL16", ["1","2"], [], {"1":"1","2":"2"}, "HC49")
G.D("L7805",  ["IN","GND","OUT"], [], {"IN":"1","GND":"2","OUT":"3"}, "TO220")
G.D("HDR6",   [str(k) for k in range(1,7)], [], {str(k):str(k) for k in range(1,7)}, "HDR6")
G.D("HDR2",   ["1","2"], [], {"1":"1","2":"2"}, "HDR2")

# ---- parts: ref -> (device, value) ---------------------------------------------
parts = {
    "U1":("ATMEGA328","ATMEGA328P-PU"), "U2":("L7805","7805"),
    "Y1":("XTAL16","16MHZ"),
    "C1":("CAP","22P"), "C2":("CAP","22P"),            # crystal load caps
    "C3":("CAP","100N"), "C4":("CAP","100N"),          # VCC / AVCC decoupling
    "C5":("CAP","100N"),                               # DTR auto-reset cap
    "C6":("CAPP","10U"), "C7":("CAPP","10U"),          # 7805 in / out
    "R1":("RES","10K"),                                # RESET pull-up
    "R2":("RES","330R"), "R3":("RES","1K"),            # pin-13 LED / power LED
    "LED1":("LED","YEL"), "LED2":("LED","GRN"),        # pin-13 / power
    "J1":("HDR6","FTDI"), "J2":("HDR2","7-12V DC"),
}

# ---- nets: name -> [(ref, pin), ...] -------------------------------------------
n = {}
def net(name, *pins): n.setdefault(name, []).extend(pins)

net("VCC", ("U1","VCC"),("U1","AVCC"),("U2","OUT"),("J1","3"),
           ("C3","1"),("C4","1"),("C7","+"),("R1","1"),("R3","1"))
net("GND", ("U1","GND1"),("U1","GND2"),("U2","GND"),("J1","1"),("J1","2"),("J2","2"),
           ("C1","2"),("C2","2"),("C3","2"),("C4","2"),("C6","-"),("C7","-"),
           ("LED1","K"),("LED2","K"))            # C5 low side is RESET, not GND (auto-reset pulse)
net("VIN", ("J2","1"),("U2","IN"),("C6","+"))              # raw 7-12 V in -> 7805
net("RESET", ("U1","RESET"),("R1","2"),("C5","2"))         # pull-up + DTR cap
net("DTR",  ("J1","6"),("C5","1"))                         # FTDI DTR -> cap -> RESET (auto-reset)
net("RXD",  ("U1","RXD"),("J1","4"))                       # FTDI TXD -> MCU RXD
net("TXD",  ("U1","TXD"),("J1","5"))                       # MCU TXD -> FTDI RXD
net("XTAL1",("U1","XTAL1"),("Y1","1"),("C1","1"))
net("XTAL2",("U1","XTAL2"),("Y1","2"),("C2","1"))
net("D13",  ("U1","SCK"),("R2","1"))                       # PB5 = Arduino pin 13
net("LED13",("R2","2"),("LED1","A"))
net("PWRLED",("R3","2"),("LED2","A"))

# ---- schematic layout (grid; only affects the .sch drawing) --------------------
order = list(parts)
sch = {}
for i, ref in enumerate(order):
    dev, val = parts[ref]
    sch[ref] = (dev, val, 20 + (i % 5) * 45.0, 80 - (i // 5) * 45.0)

W, H = 76.2, 50.8   # 3.0" x 2.0"

# ---- board placement: ref -> (footprint bbox top-left cx, cyt) in mm -----------
# Placed to keep CONNECTED parts close (short ratsnest / air-wires). U1's XTAL,
# RESET, RXD, TXD pins are all on its LEFT column, so the crystal cluster and the
# FTDI/reset cluster hug U1's left; AVCC + the pin-13 LED sit on the right column;
# the 5 V supply lives on the right edge (DC jack). HPWL 266 mm vs 511 for the
# first pass (48% shorter) -- signal nets are all <18 mm; only VCC/GND span the
# board. Verified non-overlapping + in-bounds below; ratsnest guides routing.
PLACE = {
    "U1":(34,46),                              # ATmega, centre
    "J1":(24,47), "R1":(21.5,49), "C5":(27,44),# FTDI + reset, top-left (near pins 1-3)
    "C3":(30,36),                              # VCC decoupling (near pin 7)
    "Y1":(24,27), "C1":(28.5,24), "C2":(31.5,24),  # 16 MHz + load caps (near XTAL1/2, pins 9/10)
    "C4":(44,27), "R2":(44,20), "LED1":(57,20),    # AVCC decoupling + pin-13 LED (right column)
    "J2":(74,44), "U2":(64,44), "C6":(64,40), "C7":(68,40),  # 5 V supply, right edge
    "R3":(60,30), "LED2":(60,26),              # power LED
}

def _bbox(ref):
    w, h, ox, oy = G.fp_box(G.DEV[parts[ref][0]]["pkg"]); cx, cyt = PLACE[ref]
    return (cx, cyt - h, cx + w, cyt), (ox, oy, h)

# self-check: every part placed, in the outline, no footprint overlaps
assert set(PLACE) == set(parts), ("unplaced parts", set(parts) - set(PLACE))
for r in PLACE:
    (x0, y0, x1, y1), _ = _bbox(r)
    assert 0 <= x0 and x1 <= W and 0 <= y0 and y1 <= H, ("out of bounds", r, (x0, y0, x1, y1))
_rs = list(PLACE)
for i in range(len(_rs)):
    for j in range(i + 1, len(_rs)):
        (ax0, ay0, ax1, ay1), _ = _bbox(_rs[i]); (bx0, by0, bx1, by1), _ = _bbox(_rs[j])
        assert not (ax0 < bx1 and bx0 < ax1 and ay0 < by1 and by0 < ay1), \
            ("footprint overlap", _rs[i], _rs[j])

# element origin = bbox-top-left minus the footprint's (ox, h+oy) offset
brd = {}
for r in PLACE:
    dev, val = parts[r]; (_, _, _, _), (ox, oy, h) = _bbox(r); cx, cyt = PLACE[r]
    brd[r] = (dev, val, cx - ox, cyt - h - oy)

# half-perimeter wire length (HPWL) — the standard placement quality metric; lower
# = shorter total ratsnest. Reported so a placement edit's effect is measurable.
def _hpwl():
    pos = {}
    for r, (cx, cyt) in PLACE.items():
        pkg = G.DEV[parts[r][0]]["pkg"]; w, h, ox, oy = G.fp_box(pkg); ex, ey = cx-ox, cyt-h-oy
        for (pad, px, py, dr, di) in G.PKG[pkg]: pos[(r, pad)] = (ex+px, ey+py)
    tot = 0.0
    for name, pins in n.items():
        xs = [pos[(r, G.DEV[parts[r][0]]["pm"][pin])][0] for r, pin in pins]
        ys = [pos[(r, G.DEV[parts[r][0]]["pm"][pin])][1] for r, pin in pins]
        tot += (max(xs)-min(xs)) + (max(ys)-min(ys))
    return tot

# Only WRITE files when run as a script. Guarding this under __main__ keeps the
# module import-safe: other code (e.g. an editor reusing the device/pad defs or
# the netlist) can `import gen_arduino` without silently rewriting the .sch/.brd.
if __name__ == "__main__":
    os.makedirs(OUTDIR, exist_ok=True)
    base = os.path.join(OUTDIR, "arduino-scratch")
    title = "BREADBOARD ARDUINO (ATmega328P) - Cowork/Fusion workflow test"
    G.write_sch(base + ".sch", title, sch, n)
    G.validate(base + ".sch", sch, n)
    G.write_brd(base + ".brd", title, brd, n, {}, {}, W, H)  # placed + ratsnest
    G.validate(base + ".brd", brd, n)
    print("wrote", base + ".sch", "and", base + ".brd")
    print("parts:", len(parts), " nets:", len(n),
          " placed, no overlaps, in %gx%g mm, HPWL=%.0f mm" % (W, H, _hpwl()))
