ksr/p8x/os/commands/desk.c

/* desk.c -- the window system demo (rungs 2+3 of the GUI ladder).
 *
 * Four windows under lib_wm: SHAPES (content recorded ONCE into a
 * card-resident command list -- every repaint is CLRUN, two wire
 * bytes), TERM (a small terminal: typed input under focus), FILES (a
 * directory browser: click or arrow to select, ENTER or the OPEN
 * menu item to open -- directories navigate, .P8I files open in...)
 * and VIEW (a picture window: the image BLITs straight from its file
 * into window-local coordinates each repaint). Close boxes, a
 * Mac-style press-drag-release menu, per-window hardware clipping,
 * painter's repaint -- see man desk.
 *
 * Keys: TAB cycles windows; arrows move the top window -- except a
 * focused FILES, where they move the SELECTION and ENTER opens;
 * printable keys type into a focused TERM; Ctrl-D quits.
 */

//#use abi
//#use mem     /* GFXPRES/GTSUSP/GCONEN -- the graphics/console flags, from the memory map */

//#define GLDATA 0xFF50
//#define GLSTAT 0xFF51

//#use ptr
//#use wm
//#use dirent

/* the TERM window's text: 4 history lines + the input line, 28 cols */
char tln[140];
int tcur;

/* the FILES window: current path, entries, selection */
char cpath[64];
char fnam[130];                    /* 10 entries x 13 (NUL-terminated) */
char fdir[10];
int fcnt; int fsel;

/* the VIEW window: the open picture */
char vpath[48];
int vw; int vh;

char *wm_title(int i) {
    if (i == 0) { return "SHAPES"; }
    if (i == 1) { return "TERM"; }
    if (i == 2) { return cpath; }
    return "VIEW";
}

int drawview();

int wm_content(int i) {
    int r; int ch;
    ch = wmh[i] - 15;
    if (i == 0) {
        wgput(114); wgput(30);                /* CLRUN 30: the recorded scene */
        return 0;
    }
    if (i == 1) {
        wpen(2016);
        r = 0;
        while (r < 4) {
            wm_text(3, ch - 13 - r * 13, tln + (3 - r) * 28);
            r = r + 1;
        }
        wpen(65535);
        wm_text(3, 4, tln + 112);
        return 0;
    }
    if (i == 2) {                             /* FILES: the listing */
        r = 0;
        while (r < fcnt) {                    /* selection = yellow row;
                                                 directories = cyan */
            if (r == fsel) { wpen(65504); }
            else if (fdir[r]) { wpen(2047); }
            else { wpen(65535); }
            wm_text(4, ch - 13 - r * 13, fnam + r * 13);
            r = r + 1;
        }
        return 0;
    }
    return drawview();                        /* VIEW */
}

/* record SHAPES' scene into card list 30 -- local coords, no mapping
 * verbs inside, so it replays under WHEREVER the window sits */
int rec_shapes() {
    int cw; int ch;
    cw = wmw[0] - 2; ch = wmh[0] - 15;
    wgput(112); wgput(30);                    /* CLBEG 30 */
    wpen(63488);
    wmov(10, 10); wrect(cw - 10, ch - 10);    /* the red frame */
    wpen(65504);
    wmov(cw - 30, ch - 20); wrect(cw + 60, ch + 60); /* RECT overrun:
                                                 clipped by the card */
    wgput(113);                               /* CLEND */
    return 0;
}

int tclear() {
    int i;
    i = 0;
    while (i < 140) { tln[i] = 0; i = i + 1; }
    tln[112] = '>'; tln[113] = ' '; tcur = 2;
    return 0;
}
int tscroll() {
    int i;
    i = 0;
    while (i < 3 * 28) { tln[i] = tln[i + 28]; i = i + 1; }
    i = 0;                                    /* input -> history row 3 */
    while (i < 28) { tln[3 * 28 + i] = tln[4 * 28 + i]; i = i + 1; }
    tln[112] = '>'; tln[113] = ' '; tln[114] = 0; tcur = 2;
    return 0;
}
/* the TERM shell, one rule: the line ENTER scrolled into history is
 * a PROGRAM INVOCATION -- "paint.bin", "/bin/cube.bin", args and all
 * -- launched exactly like a click in FILES (SYS_EXEC, chained with
 * -d). Navigation is FILES' job; the window IS dir, the Mac way. */
int tcmd() {
    char *c;
    c = tln + 86;
    while (*c == 32) { c = c + 1; }
    if (c[0] != 0) { runbin(c); }
    return 0;
}

int tkey(int k) {
    if (k == 13 || k == 10) { tscroll(); tcmd(); wm_repaint(); return 0; }
    if (k == 8 || k == 127) {
        if (tcur > 2) { tcur = tcur - 1; tln[112 + tcur] = 0; wm_repaint(); }
        return 0;
    }
    if (k >= 32 && k < 127 && tcur < 27) {
        tln[112 + tcur] = k; tln[113 + tcur] = 0; tcur = tcur + 1;
        wm_repaint();
    }
    return 0;
}

/* ---- the FILES browser ------------------------------------------------------ */
int tprint(char *s) {                         /* a line into TERM's history */
    int i;
    tscroll();
    i = 0;
    while (s[i] != 0 && i < 27) { tln[3 * 28 + i] = s[i]; i = i + 1; }
    tln[3 * 28 + i] = 0;
    return 0;
}

int fscan() {                                 /* read cpath's entries */
    int r; int j; int k;
    fcnt = 0; fsel = 0;
    r = bios(FOPENDIR, cpath, 0);
    if (r & 256) { return 1; }
    r = bios(FNEXT, 0, 0);
    while ((r & 256) == 0 && fcnt < 10) {
        de_read();
        /* keep real files and dirs whose name STARTS PRINTABLE -- this
         * skips '.', deleted slots ($E5 first byte: FNEXT yields them,
         * and TEXT would draw an undefined glyph as a silent skip, a
         * phantom empty row) and the volume slot -- but keeps '..' */
        j = de[0] & 255;
        if ((de_isfile() || de_isdir()) && j >= 33 && j <= 126 &&
            (de_isdot() == 0 || (de[1] & 255) == '.')) {
            j = 0; k = fcnt * 13;
            while (j < 12) {
                if ((de[j] & 255) > 32) { fnam[k] = de[j]; k = k + 1; }
                j = j + 1;
            }
            fnam[k] = 0;
            if (k > fcnt * 13) {              /* a non-empty name only */
                fdir[fcnt] = de_isdir();
                fcnt = fcnt + 1;
            }
        }
        r = bios(FNEXT, 0, 0);
    }
    return 0;
}

int scopy(char *d, char *c, int cap) {        /* bounded strcpy */
    int i;
    i = 0;
    while (c[i] != 0 && i < cap) { d[i] = c[i]; i = i + 1; }
    d[i] = 0;
    return 0;
}

/* a short status line into TERM's history, then repaint (the ?EXEC/?OPEN
 * failure tail -- factored so each site costs one call, not three) */
int fail(char *s) { tprint(s); wm_repaint(); return 0; }
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
